keithstrachan/Tiny-M/STLs/essentials/Gantry/Front-Idler/readme.md

# Front Idler V4  

- optimzed belt path
- fixed printing 0.2 layer high

## BOM  
4 x F695-2RS  
2 x DIN 912 M5x40  
2 x ISO 7380-1 V2 M5x35  
2 x M5 T-Nut  
2 x ISO 7380-1 M5x16  

**Washer Variante 1:**  
4 x DIN 988 5x10x1 Shim Ring  

**Washer Variante 2:**   (0.5mm washer between bearings):  
2 x DIN 988 5x8x0.5 Shim Ring  
4 x DIN 988 5x8x0.75 Shim Ring
