keithstrachan/Tiny-M/images/v4_toolhead.jpg

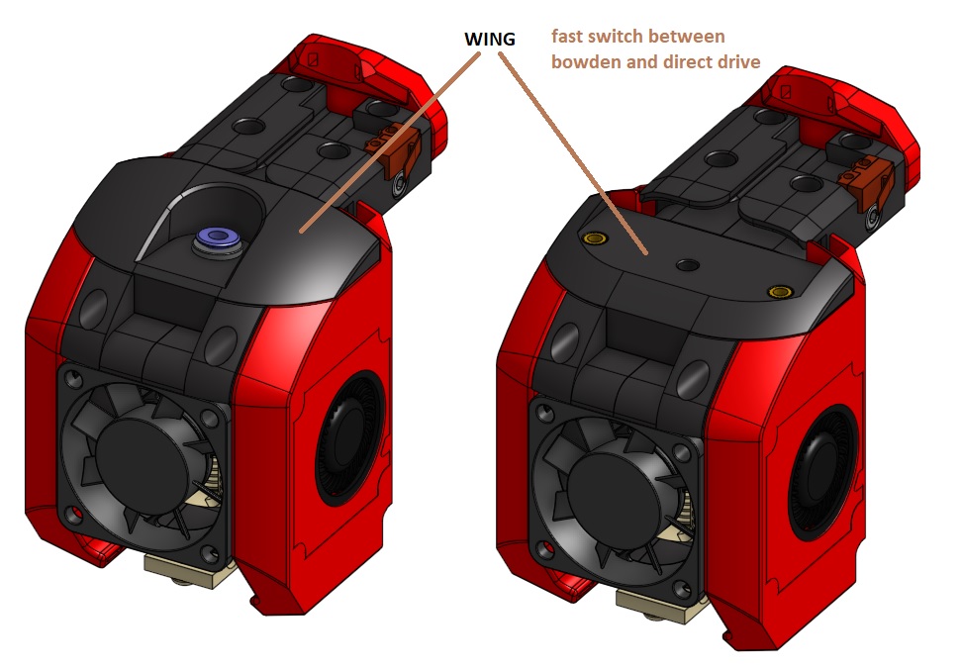
images/v4_toolhead.jpg
