keithstrachan/Tiny-M/usermods/almost_all_metal_undercarriage_with_purge_bucket/Images/image_under_1.jpg

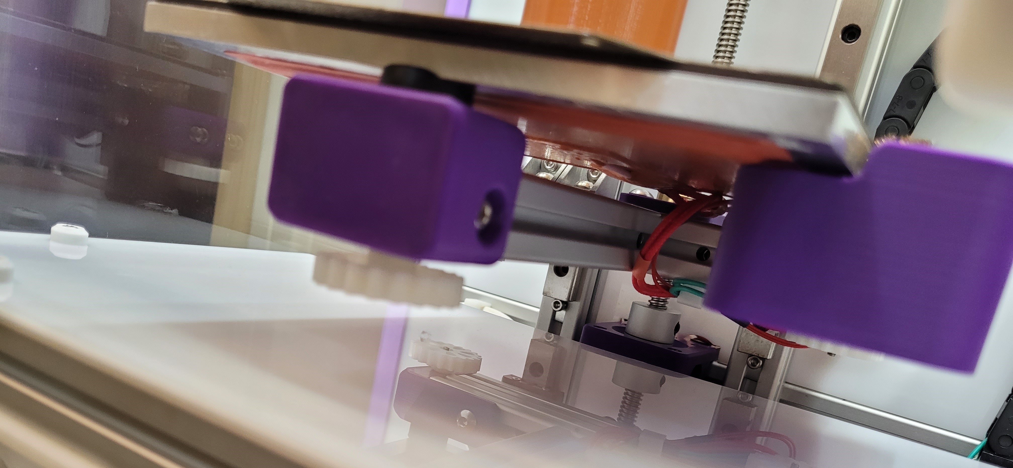
usermods/almost_all_metal_undercarriage_with_purge_bucket/Images/image_under_1.jpg
