keithstrachan/Tiny-M/usermods/belted_z_mod/Images/Above bed.jpg

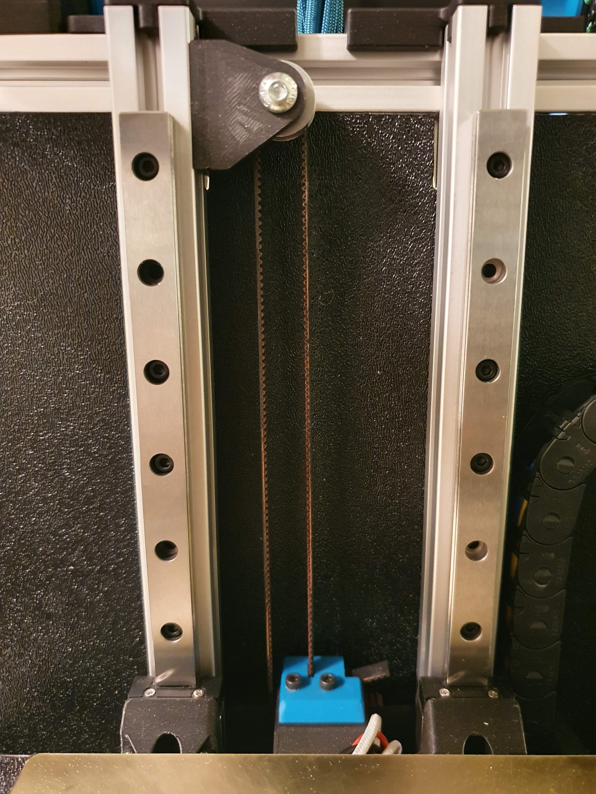
usermods/belted_z_mod/Images/Above bed.jpg
