keithstrachan/Tiny-M/usermods/belted_z_mod/Images/CAD front.png

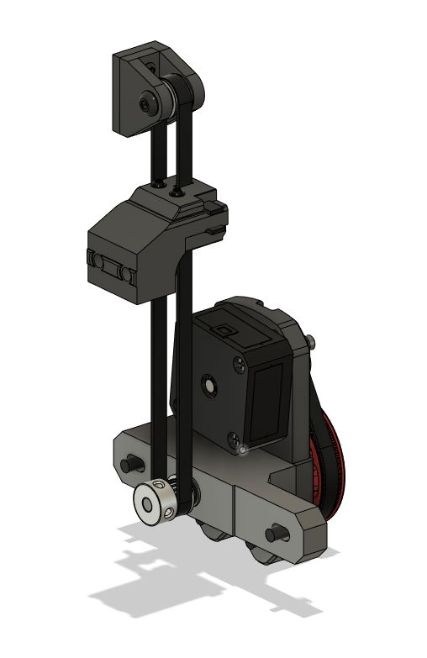
usermods/belted_z_mod/Images/CAD front.png
