keithstrachan/Tiny-M/usermods/belted_z_mod/Images/Motor.jpg

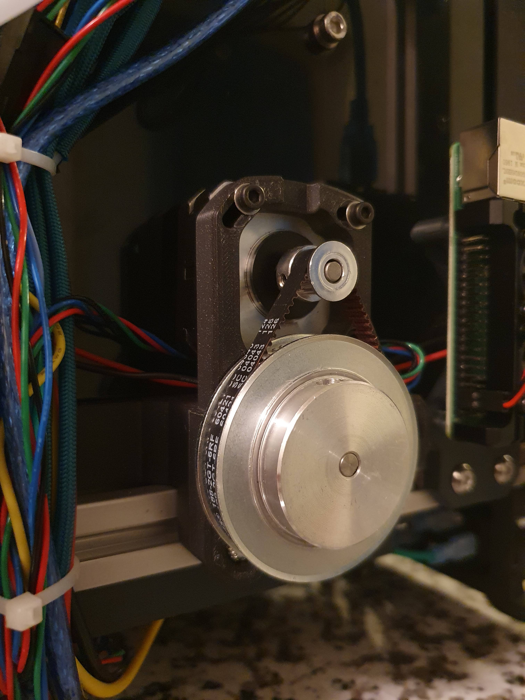
usermods/belted_z_mod/Images/Motor.jpg
