keithstrachan/Tiny-M/usermods/high_torque_belted_z/images/20210530_182317.jpg

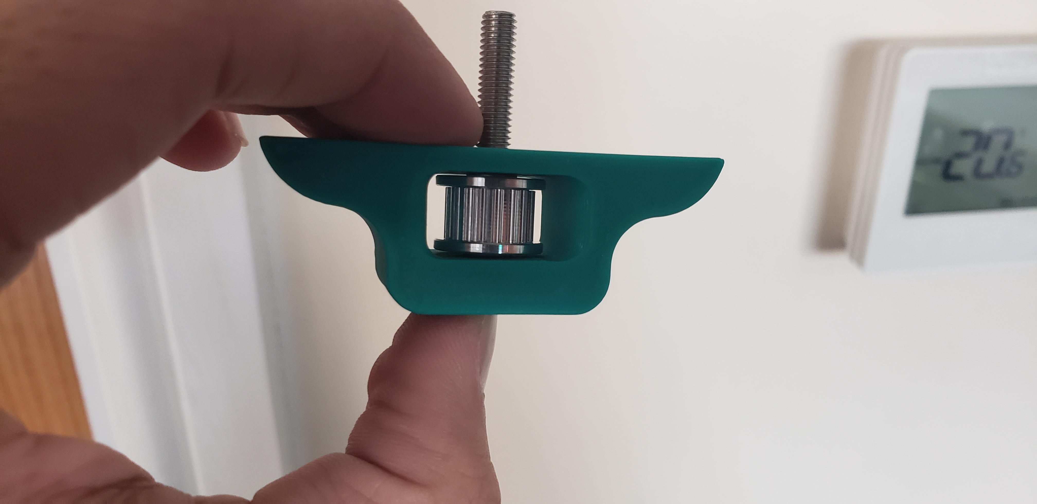
usermods/high_torque_belted_z/images/20210530_182317.jpg
