keithstrachan/Tiny-M/usermods/high_torque_belted_z/images/20210605_135525.jpg

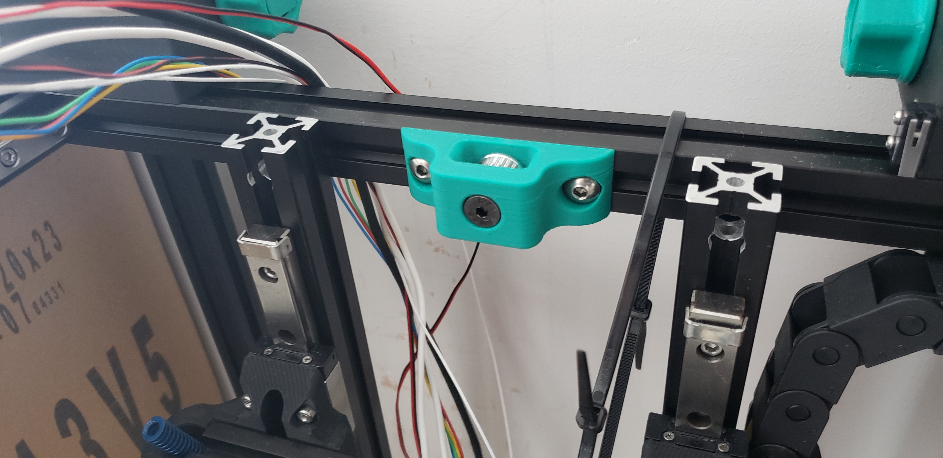
usermods/high_torque_belted_z/images/20210605_135525.jpg
