keithstrachan/Tiny-M/usermods/high_torque_belted_z/images/20210607_204112.jpg

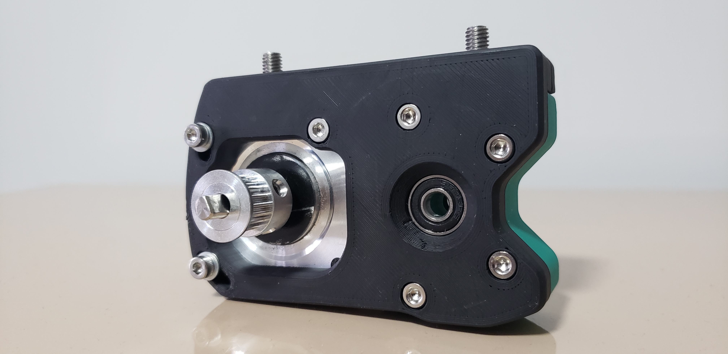
usermods/high_torque_belted_z/images/20210607_204112.jpg
