keithstrachan/Tiny-M/usermods/high_torque_belted_z/images/20210608_170528.jpg

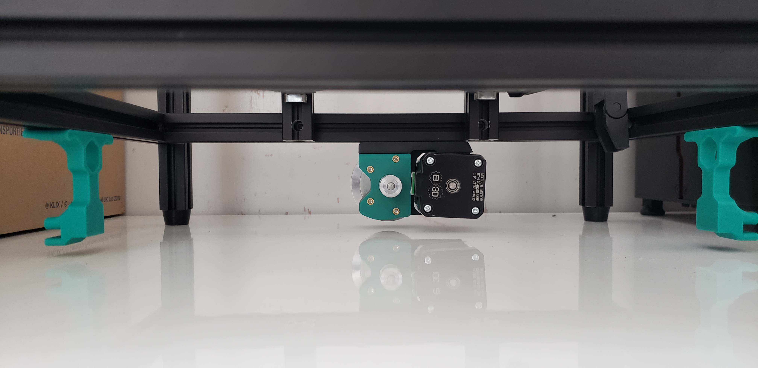
usermods/high_torque_belted_z/images/20210608_170528.jpg
