keithstrachan/Tiny-M/usermods/high_torque_belted_z/images/20210608_170559.jpg

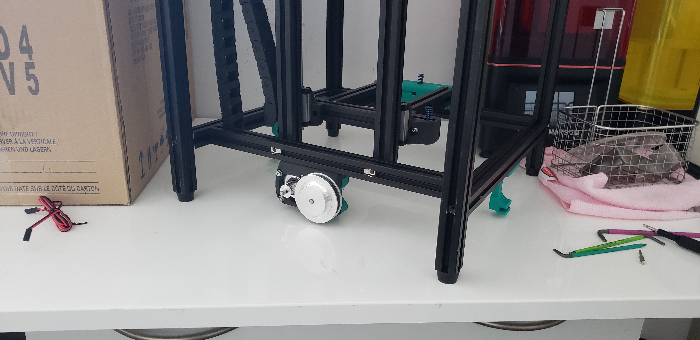
usermods/high_torque_belted_z/images/20210608_170559.jpg
