keithstrachan/Tiny-M/usermods/high_torque_belted_z/images/20210618_183542.jpg

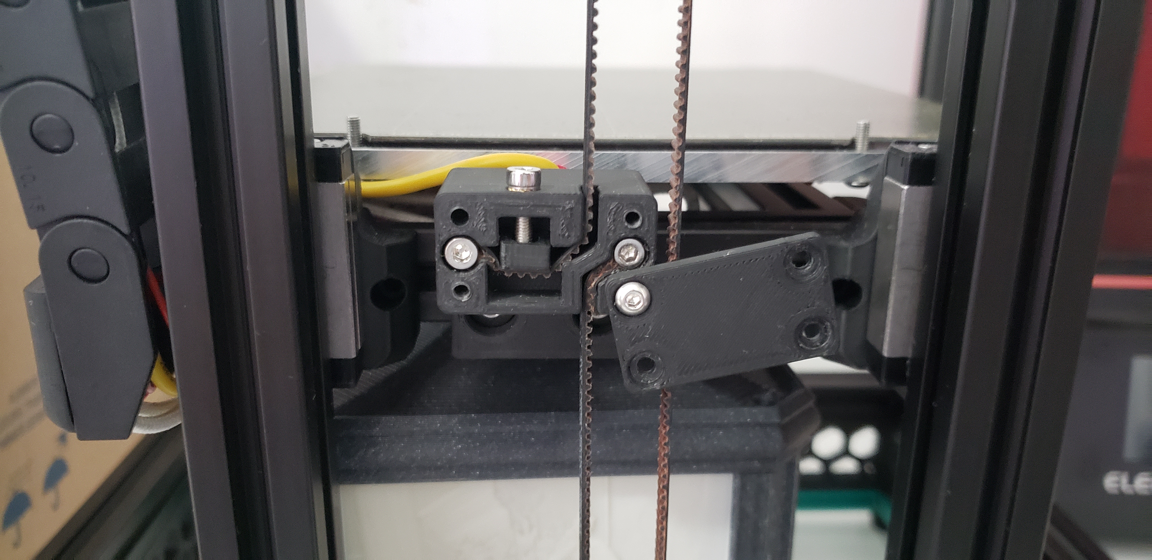
usermods/high_torque_belted_z/images/20210618_183542.jpg
