keithstrachan/Tiny-M/usermods/high_torque_belted_z/images/Fusion360_Lnw4iSIMuG.png

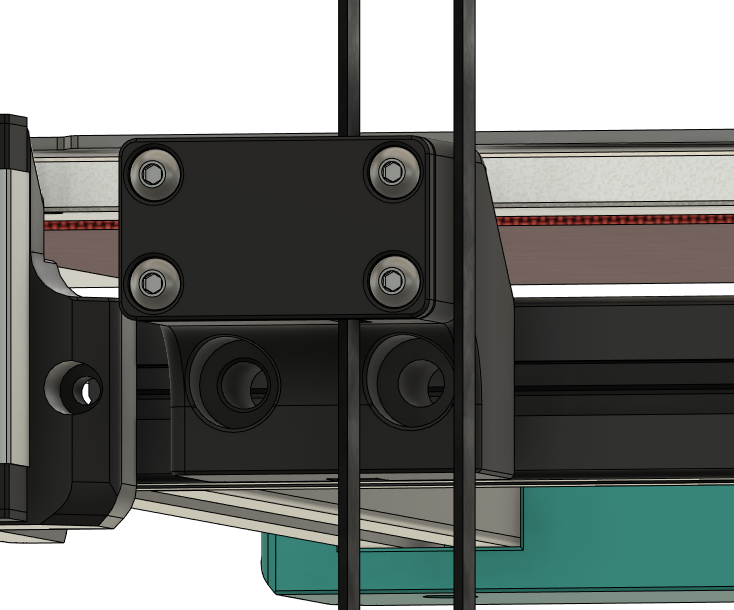
usermods/high_torque_belted_z/images/Fusion360_Lnw4iSIMuG.png
