keithstrachan/Tiny-M/usermods/DrillGuides/tiny-m_drill_guide.step.step

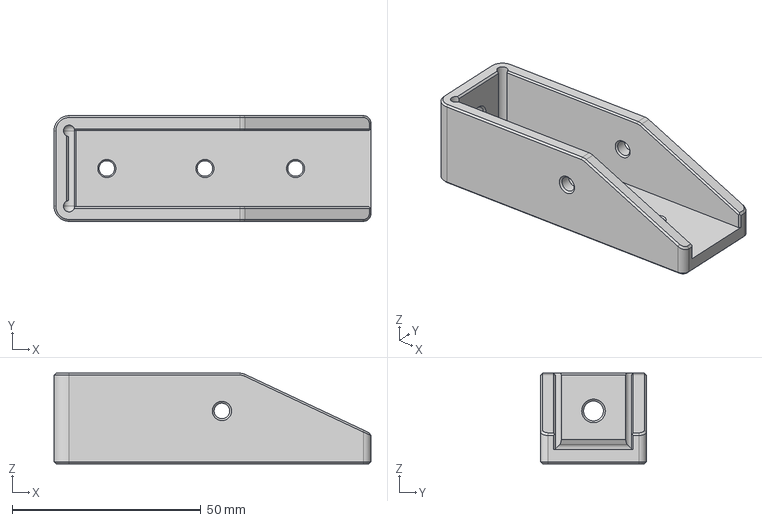
[picture p43: CAD file, 2021-09-06]
usermods/DrillGuides/tiny-m_drill_guide.step.step
84.0 x 28.0 x 24.0 mm
