keithstrachan/Tiny-M/usermods/front_bed_mount_proud_text.stl

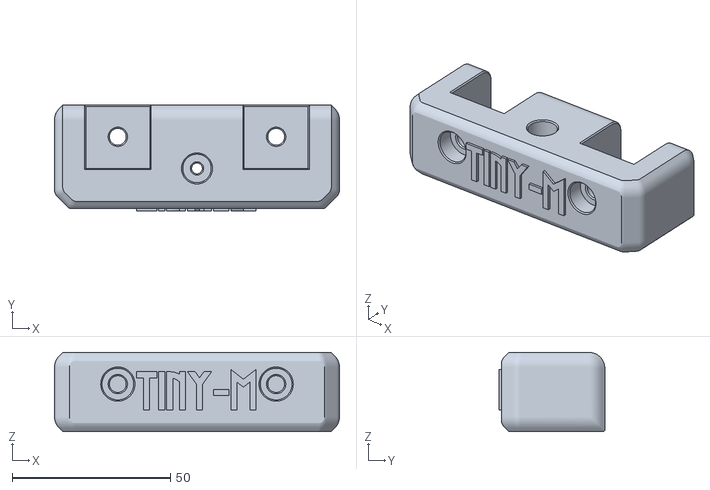
[picture p44: CAD file, 2021-03-21]
usermods/front_bed_mount_proud_text.stl
90.0 x 33.4 x 25.0
