keithstrachan/Tiny-M/usermods/high_torque_belted_z/STLs/150mm ver/beltztens150.stl

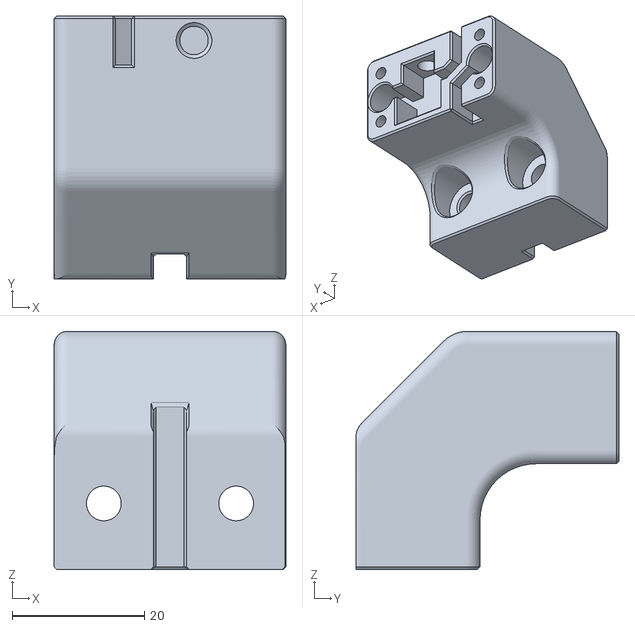
[picture p45: CAD file, 2021-12-28]
usermods/high_torque_belted_z/STLs/150mm ver/beltztens150.stl
35.0 x 39.7 x 36.0
