keithstrachan/Tiny-M/usermods/high_torque_belted_z/STLs/[a]_upper_idler.stl

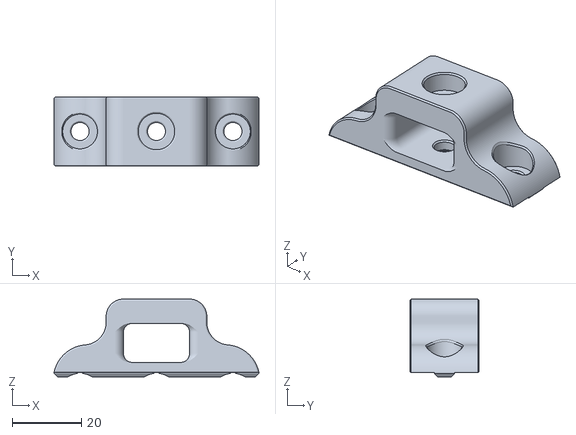
[picture p46: CAD file, 2021-09-06]
usermods/high_torque_belted_z/STLs/[a]_upper_idler.stl
59.0 x 20.0 x 22.4
