keithstrachan/Tiny-M/usermods/mgn12_x_rail/Tiny-M_Umbilical_Frame.stl

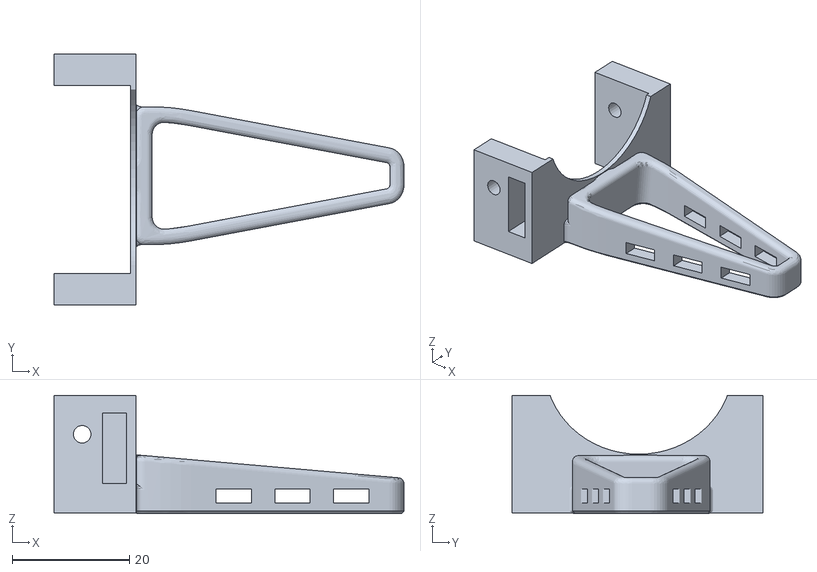
[picture p47: CAD file, 2021-03-21]
usermods/mgn12_x_rail/Tiny-M_Umbilical_Frame.stl
59.6 x 42.7 x 20.1
