keithstrachan/Tiny-M/usermods/rear_cable_guide/right-back-cable-holder-honeycomb.stl

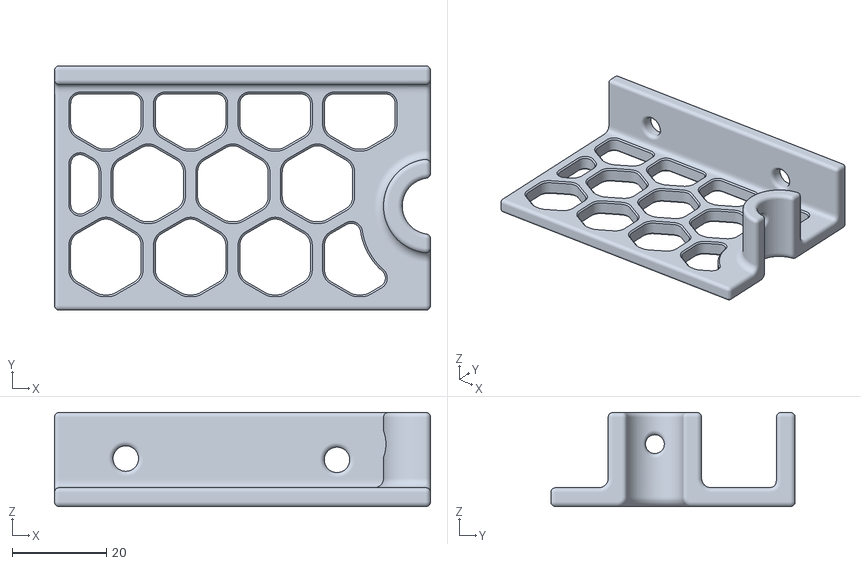
[picture p48: CAD file, 2021-04-13]
usermods/rear_cable_guide/right-back-cable-holder-honeycomb.stl
80.0 x 52.0 x 20.0
