keithstrachan/Tiny-M/usermods/Tiny-dooM/STL/DoomCap.stl

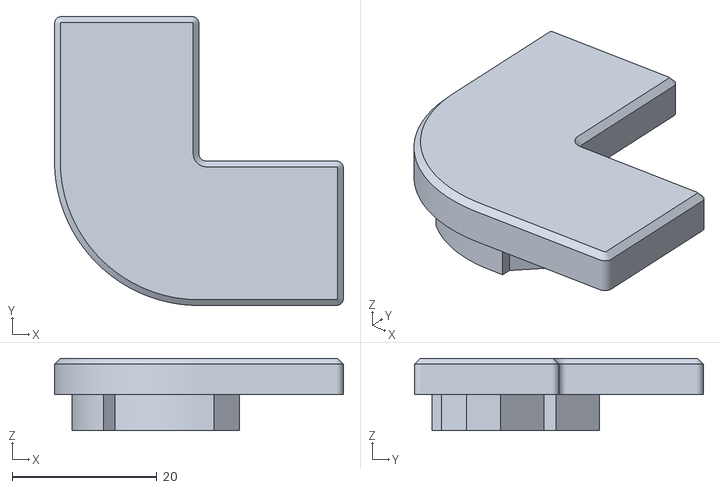
[picture p49: CAD file, 2021-05-16]
usermods/Tiny-dooM/STL/DoomCap.stl
40.0 x 40.0 x 10.0
