keithstrachan/Tiny-M/usermods/triple_z_belted/STL/motor_mount_x3.stl

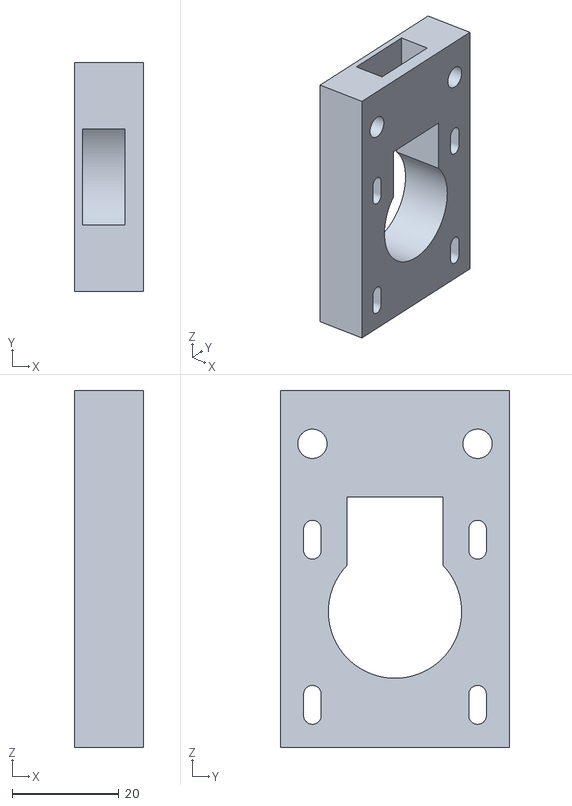
[picture p50: CAD file, 2021-05-16]
usermods/triple_z_belted/STL/motor_mount_x3.stl
13.0 x 43.0 x 67.0
