keithstrachan/Tiny-M/usermods/Xile_Mods/Buck_Converter_Mount/Buck_Converter_Mount.STL

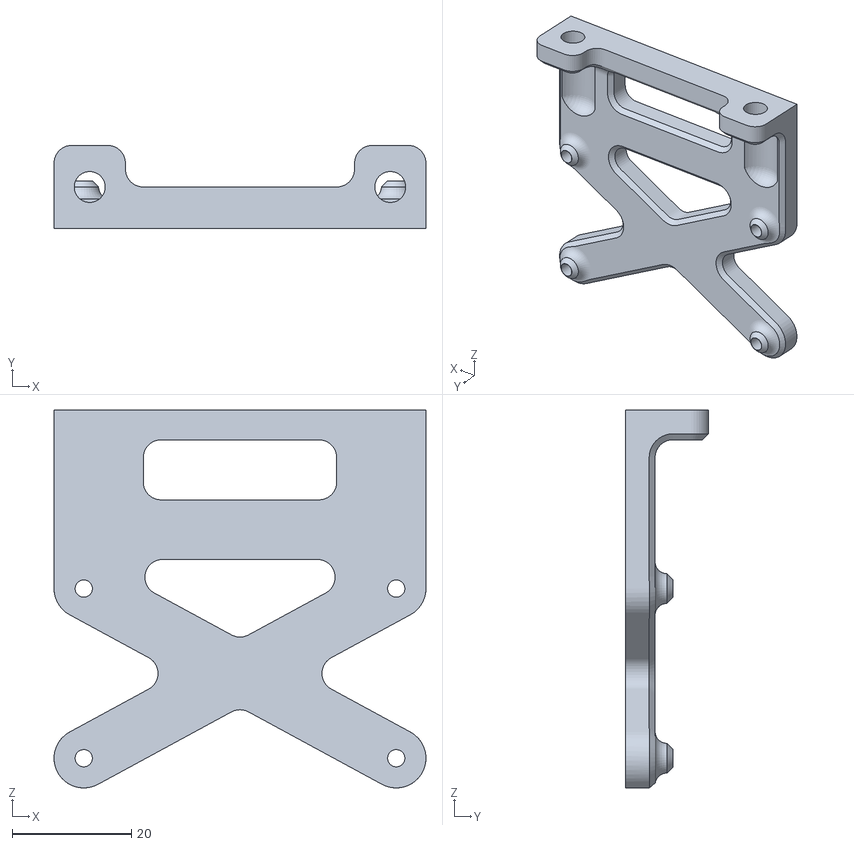
[picture p51: CAD file, 2021-03-21]
usermods/Xile_Mods/Buck_Converter_Mount/Buck_Converter_Mount.STL
62.5 x 14.0 x 63.5
