keithstrachan/Tiny-M/usermods/Xile_Mods/Cover_No_Logo.stl

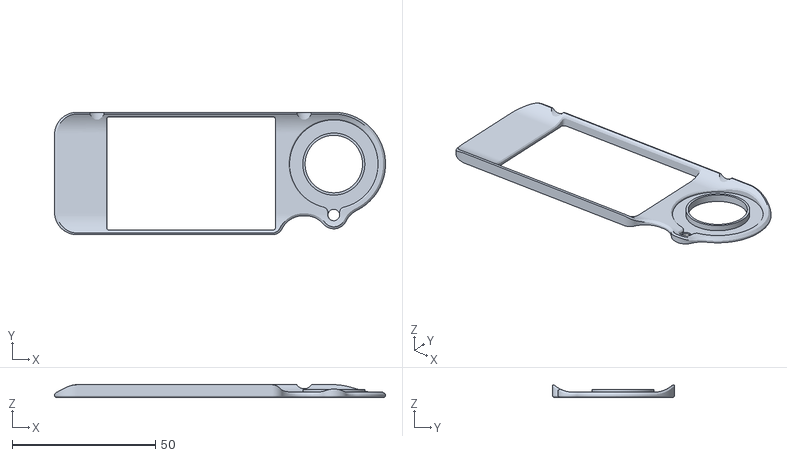
[picture p52: CAD file, 2021-03-21]
usermods/Xile_Mods/Cover_No_Logo.stl
115.4 x 42.6 x 4.42
