keithstrachan/Tiny-M/usermods/Xile_Mods/LRS-150_Mount/LRS-150_Mount.STL

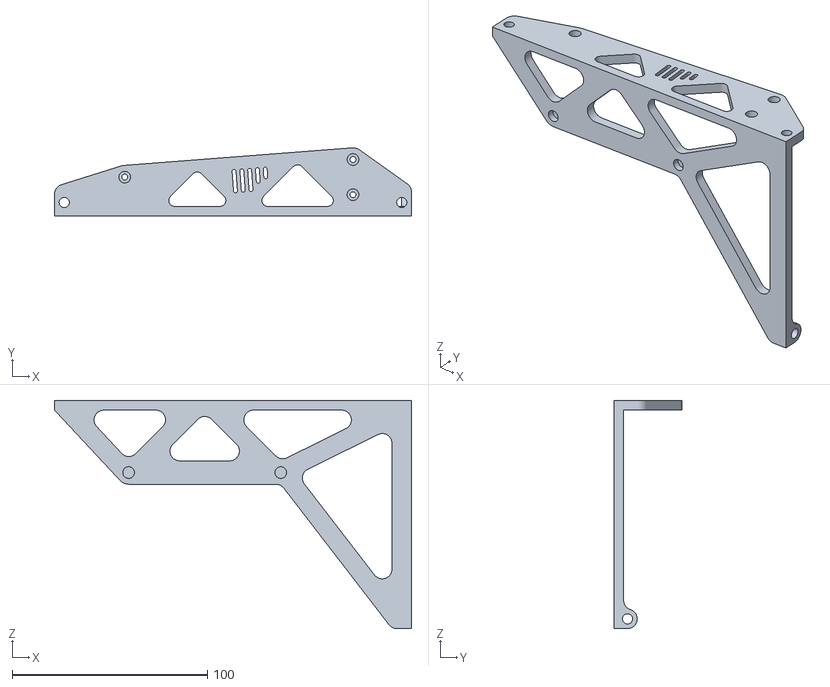
[picture p53: CAD file, 2021-03-21]
usermods/Xile_Mods/LRS-150_Mount/LRS-150_Mount.STL
183.0 x 35.0 x 117.0
