keithstrachan/Tiny-M/usermods/Xile_Mods/Panel Mounting/PanelClip_v2_1.stl

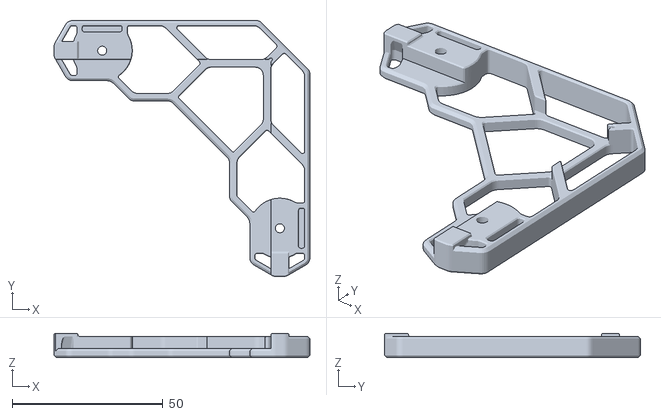
[picture p54: CAD file, 2021-03-21]
usermods/Xile_Mods/Panel Mounting/PanelClip_v2_1.stl
85.0 x 85.0 x 8.10
