keithstrachan/Tiny-M/usermods/Xile_Mods/Raised_ABdrives/ab_drive_top_raised.STL

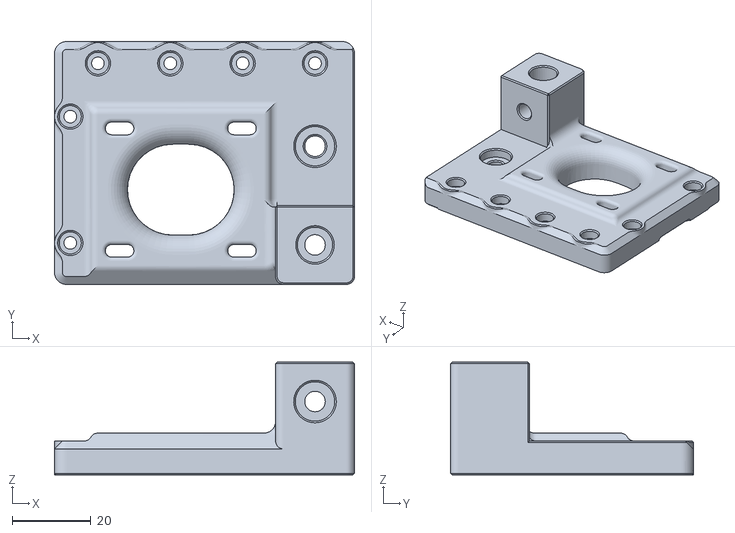
[picture p55: CAD file, 2021-03-21]
usermods/Xile_Mods/Raised_ABdrives/ab_drive_top_raised.STL
76.0 x 61.5 x 28.6
