keithstrachan/Tiny-M/usermods/Xile_Mods/Raspi_Mount/Raspi_Mount.STL

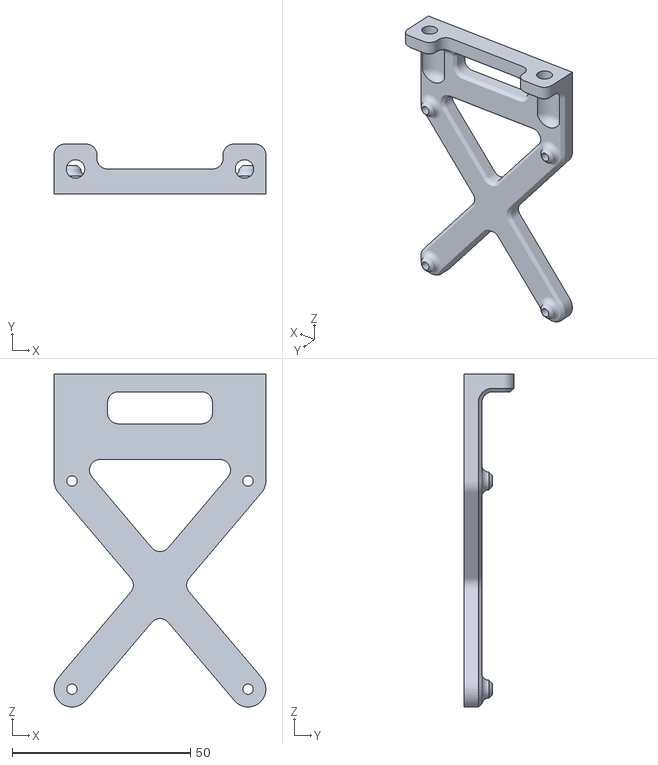
[picture p56: CAD file, 2021-03-21]
usermods/Xile_Mods/Raspi_Mount/Raspi_Mount.STL
59.4 x 14.0 x 93.4
