keithstrachan/Tiny-M/usermods/Xile_Mods/SKR_Mini_Mount/SKR_Mini_Mount.STL

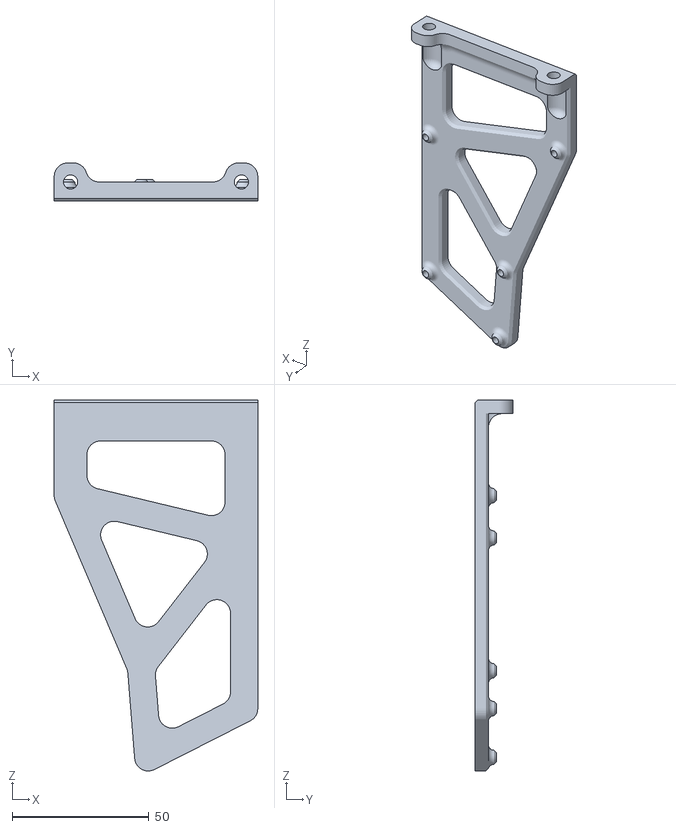
[picture p57: CAD file, 2021-03-21]
usermods/Xile_Mods/SKR_Mini_Mount/SKR_Mini_Mount.STL
74.5 x 14.0 x 135.8
