keithstrachan/Tiny-M/usermods/Xile_Mods/Tensioning_Wrench/Knob_Wrench.stl

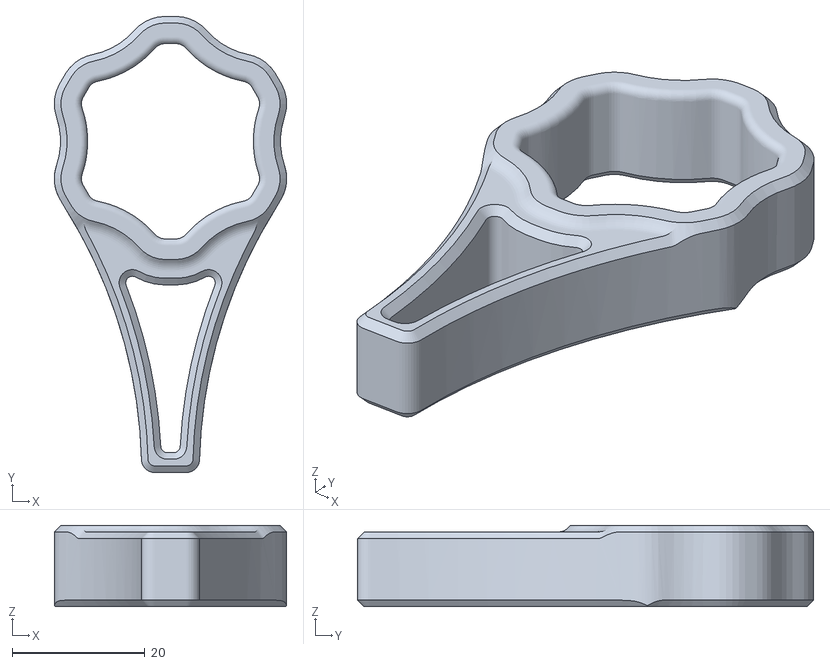
[picture p58: CAD file, 2021-03-21]
usermods/Xile_Mods/Tensioning_Wrench/Knob_Wrench.stl
35.1 x 68.8 x 12.3
