keithstrachan/Tiny-M/CAD/V4/Drill Tap Jigs v4.step

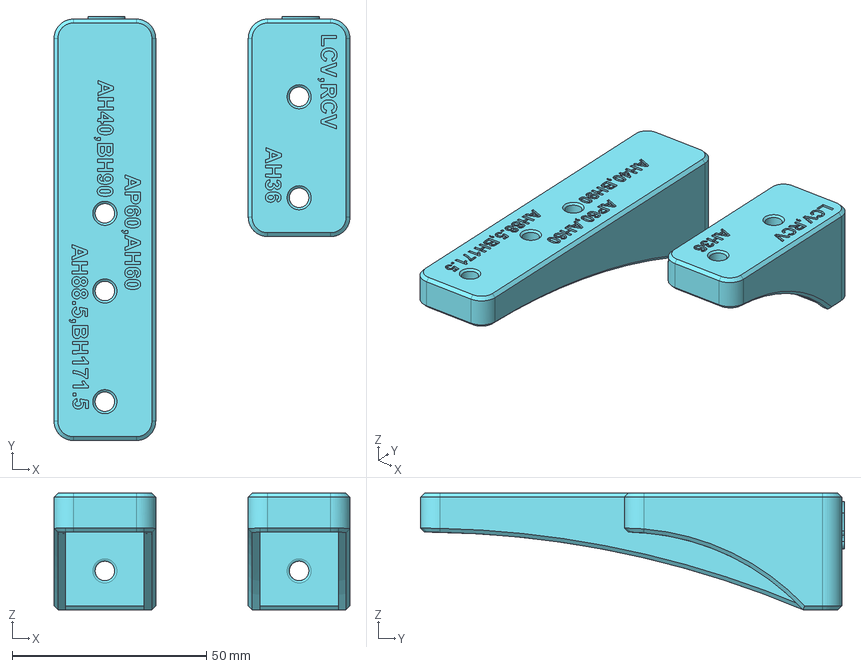
[picture p59: CAD file, 2021-05-12]
CAD/V4/Drill Tap Jigs v4.step
76.2 x 109.2 x 30.0 mm
