keithstrachan/Tiny-M/STLs/essentials/Bed/z_position_lower.stl

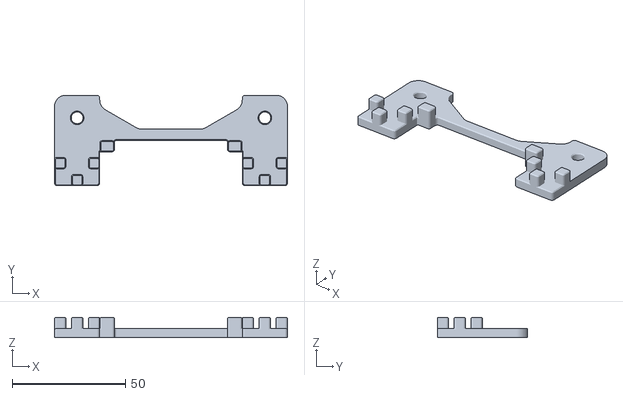
[picture p60: CAD file, 2021-05-06]
STLs/essentials/Bed/z_position_lower.stl
103.0 x 40.0 x 9.00
