keithstrachan/Tiny-M/STLs/essentials/Gantry/X_Axis/X_Carriage/mini_AB_parts/printed_parts_MGN12_v4 - mini_ab - latch_shuttle.stl

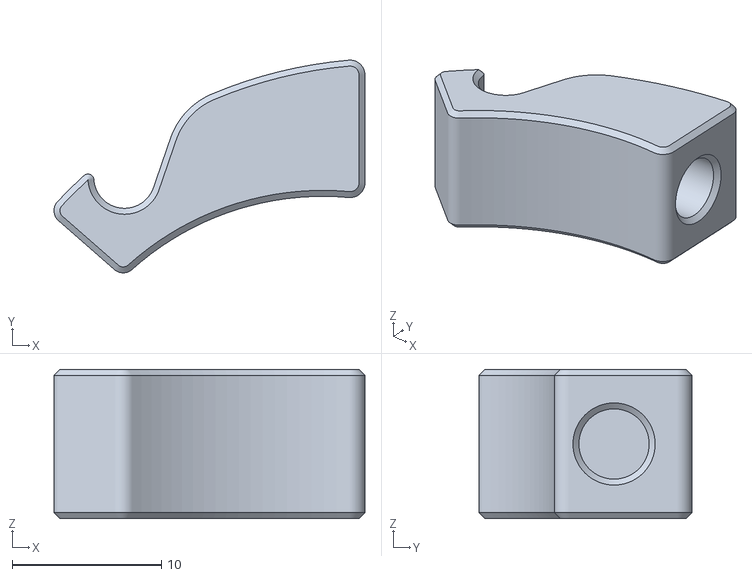
[picture p61: CAD file, 2021-05-06]
STLs/essentials/Gantry/X_Axis/X_Carriage/mini_AB_parts/printed_parts_MGN12_v4 - mini_ab - latch_shuttle.stl
20.8 x 14.2 x 10.0
