keithstrachan/Tiny-M/STLs/essentials/Gantry/X_Axis/X_Carriage/x-carriage_belt_clamp.stl

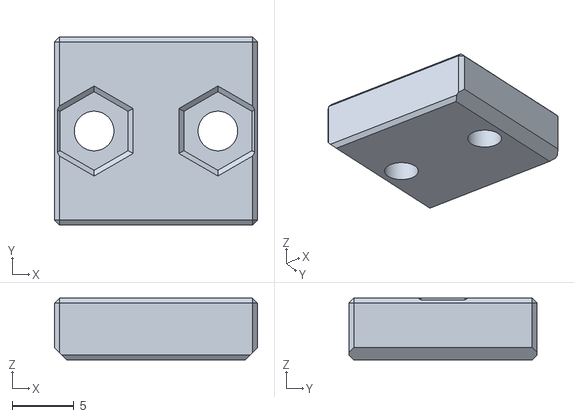
[picture p62: CAD file, 2021-05-06]
STLs/essentials/Gantry/X_Axis/X_Carriage/x-carriage_belt_clamp.stl
16.4 x 15.2 x 5.00
