keithstrachan/Tiny-M/STLs/essentials/Tools/Drill_Tap_Jig_A_.stl

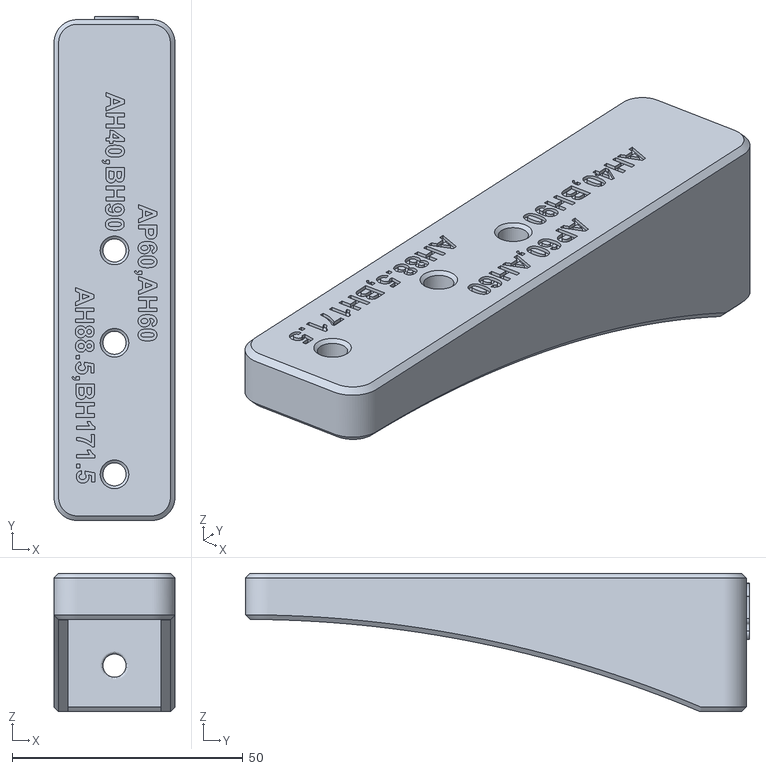
[picture p63: CAD file, 2021-05-12]
STLs/essentials/Tools/Drill_Tap_Jig_A_.stl
26.2 x 109.2 x 30.0
