keithstrachan/Tiny-M/usermods/190mm_prusa_mini_mod/STLs/[a]_side_skirt_right_x2.stl

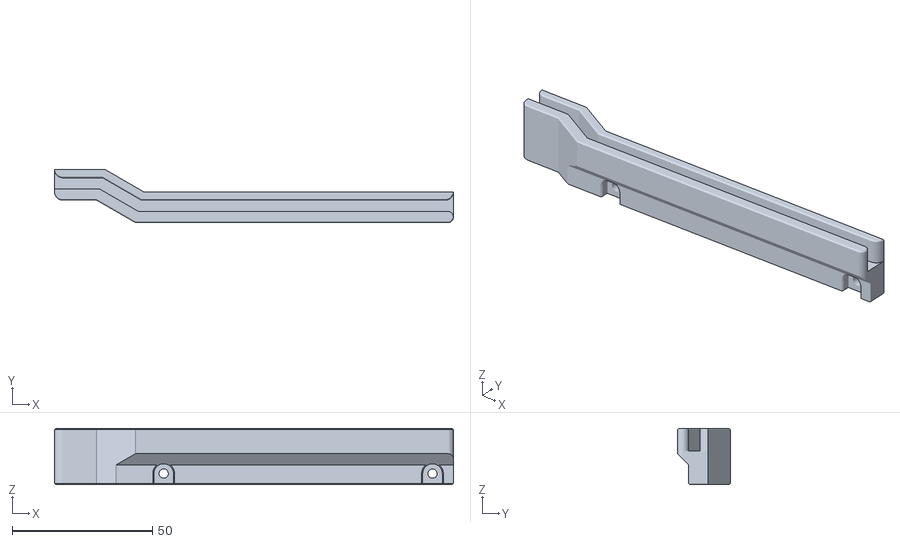
[picture p64: CAD file, 2021-05-06]
usermods/190mm_prusa_mini_mod/STLs/[a]_side_skirt_right_x2.stl
142.5 x 19.0 x 20.0
