keithstrachan/Tiny-M/usermods/2020_Hinged_TopHat_Print/2020_Hinged_TopHat_Print_Hinge Mid 2 Print.stl

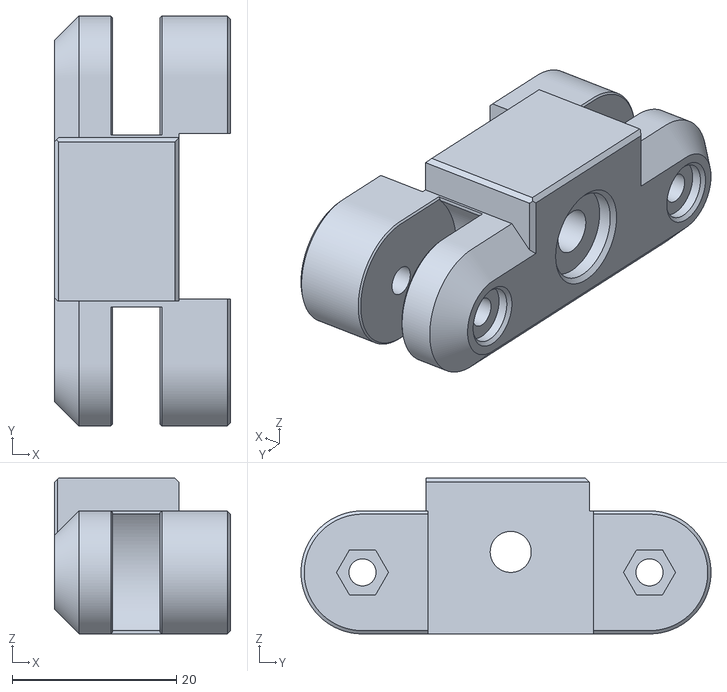
[picture p65: CAD file, 2021-03-21]
usermods/2020_Hinged_TopHat_Print/2020_Hinged_TopHat_Print_Hinge Mid 2 Print.stl
21.5 x 50.0 x 19.0
