keithstrachan/Tiny-M/usermods/5mm_idler_pins/CAD/front_idler_right_V4_5mm_Pin v3.step

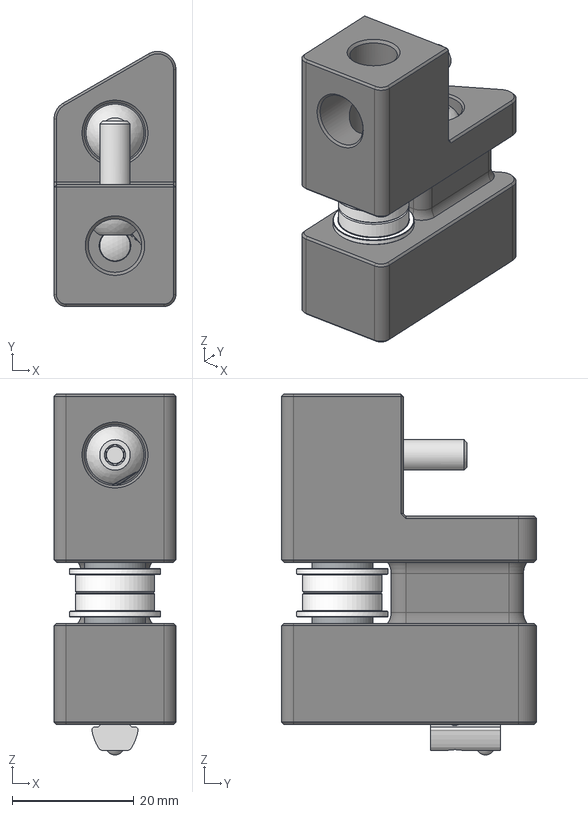
[picture p66: CAD file, 2021-03-31]
usermods/5mm_idler_pins/CAD/front_idler_right_V4_5mm_Pin v3.step
20.0 x 41.8 x 59.2 mm
F695-2RS x 2
ISO 7380-1 M5x35
DIN 988 5x10x1 Shim Ring x 2
front_idler_right_bottom_V4
M5x16
M5-T-Nut
front_idler_right_top_V4
91595A376_32mm_METRIC ALLOY STEEL DOWEL PIN
