keithstrachan/Tiny-M/usermods/all_metal_bed_undercarriage/CAD/190_bed.step

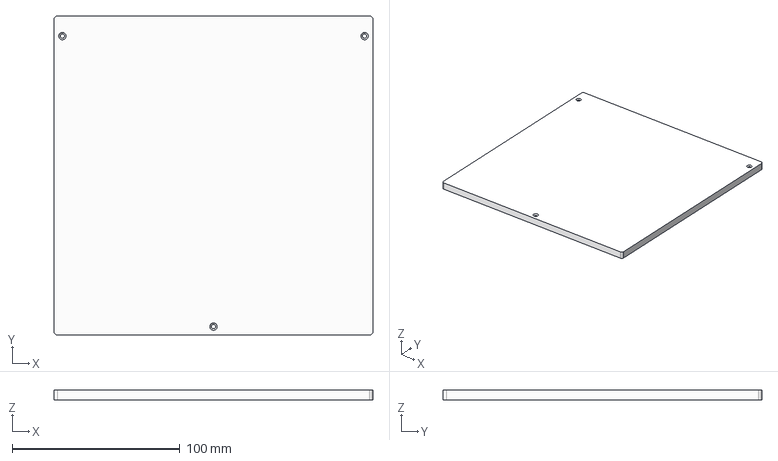
[picture p67: CAD file, 2021-05-21]
usermods/all_metal_bed_undercarriage/CAD/190_bed.step
190.0 x 190.0 x 6.00 mm
