keithstrachan/Tiny-M/usermods/all_metal_bed_undercarriage/STL/middle_jig.stl

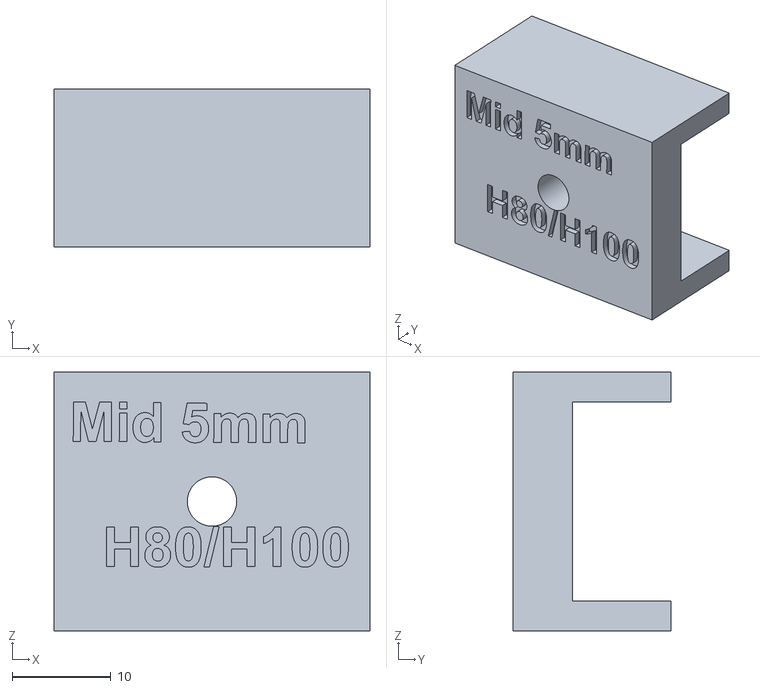
[picture p68: CAD file, 2021-05-21]
usermods/all_metal_bed_undercarriage/STL/middle_jig.stl
32.0 x 16.0 x 26.2
