keithstrachan/Tiny-M/usermods/almost_all_metal_undercarriage_with_purge_bucket/STLs/bed_right_mount.3mf

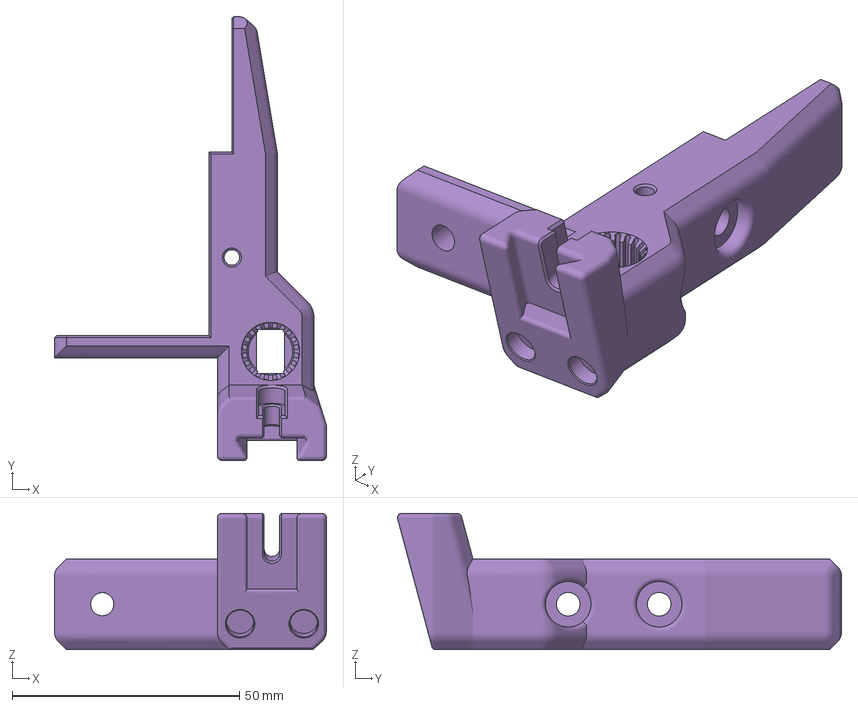
[picture p69: CAD file, 2021-12-28]
usermods/almost_all_metal_undercarriage_with_purge_bucket/STLs/bed_right_mount.3mf
59.8 x 97.6 x 30.0 mm
