keithstrachan/Tiny-M/usermods/belted_z_mod/STLs/Pancake Stepper Bracket.stl

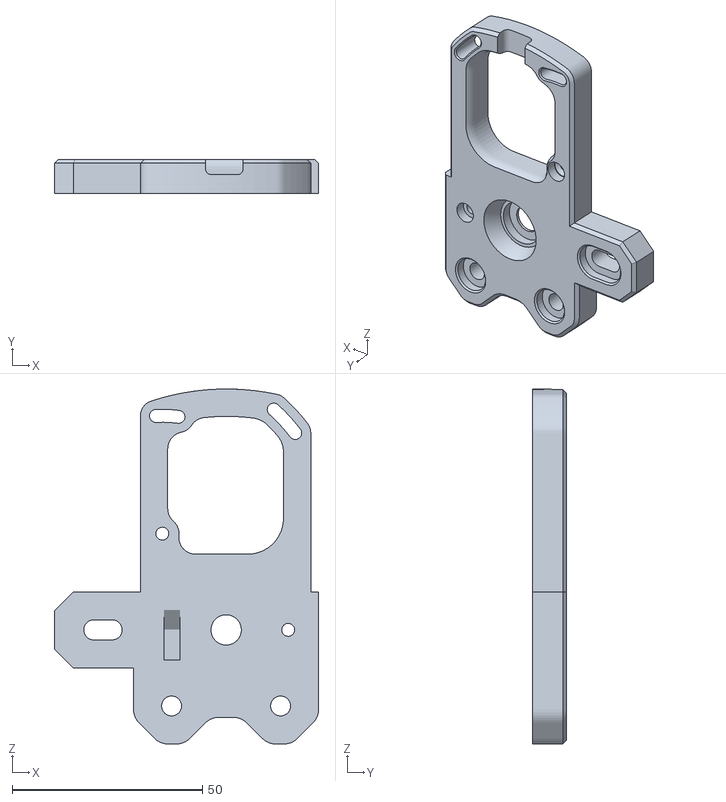
[picture p70: CAD file, 2021-05-12]
usermods/belted_z_mod/STLs/Pancake Stepper Bracket.stl
69.5 x 9.00 x 93.3
