keithstrachan/Tiny-M/usermods/door_handle/stl/Door_Handle.stl

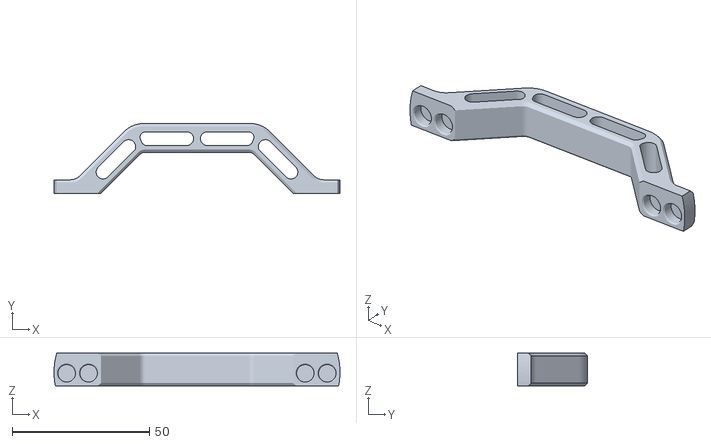
[picture p71: CAD file, 2022-09-30]
usermods/door_handle/stl/Door_Handle.stl
104.3 x 25.5 x 12.0
