keithstrachan/Tiny-M/usermods/DrillGuides/tiny-m_tap_guide.step

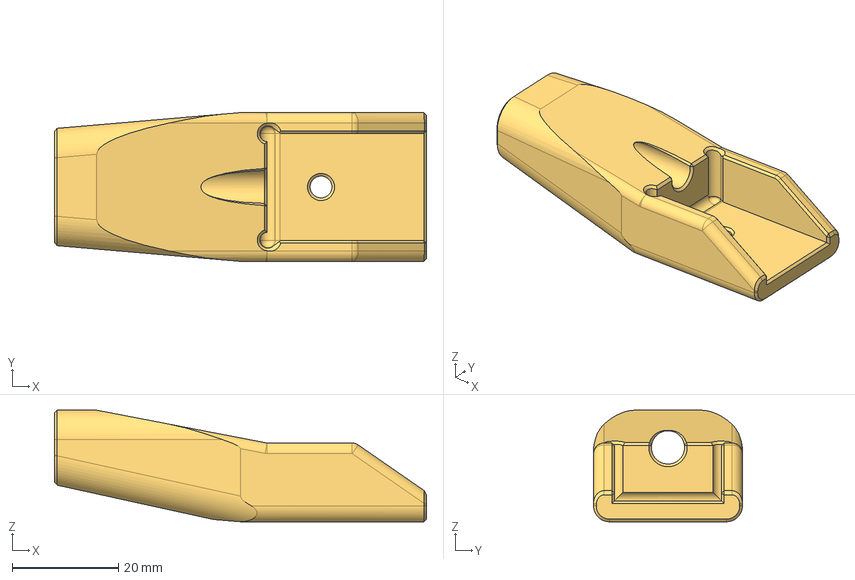
[picture p72: CAD file, 2021-09-06]
usermods/DrillGuides/tiny-m_tap_guide.step
70.0 x 28.0 x 21.0 mm
