keithstrachan/Tiny-M/usermods/high_torque_belted_z/STLs/150mm ver/idlerm5p2.stl

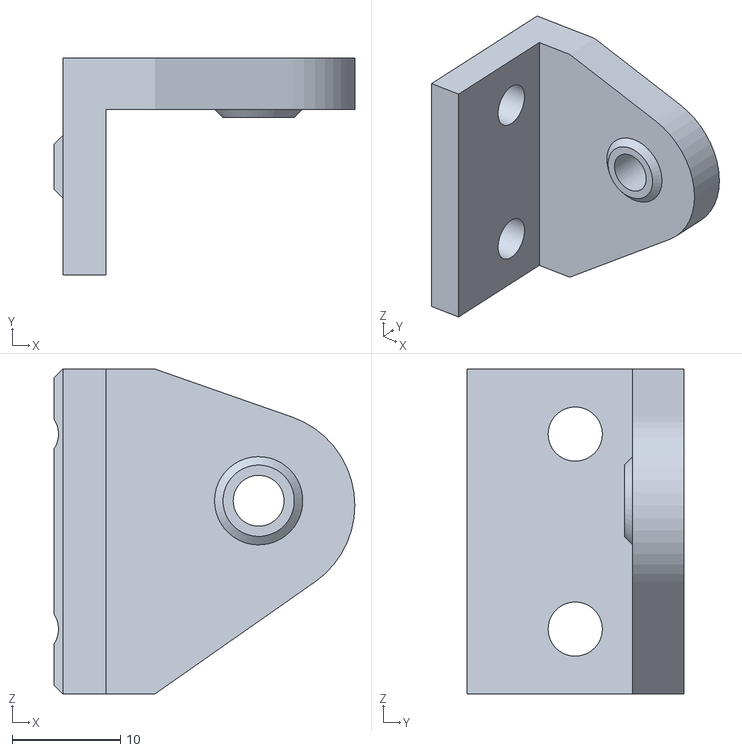
[picture p73: CAD file, 2021-12-28]
usermods/high_torque_belted_z/STLs/150mm ver/idlerm5p2.stl
27.8 x 20.0 x 30.0
