keithstrachan/Tiny-M/usermods/high_torque_belted_z/STLs/[a]_tension_plate.stl

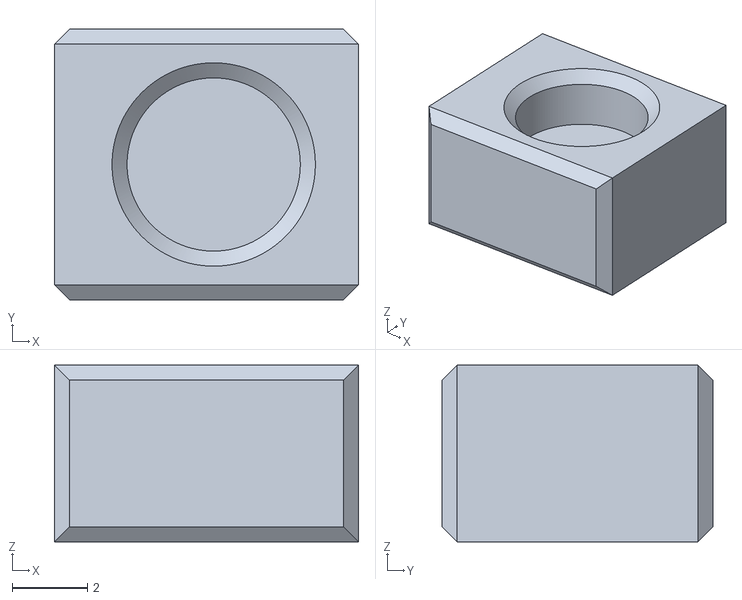
[picture p74: CAD file, 2021-09-06]
usermods/high_torque_belted_z/STLs/[a]_tension_plate.stl
8.07 x 7.20 x 4.70
