keithstrachan/Tiny-M/usermods/mgn12_x_rail/Tiny-M_Extruder_for_Sherpa_Mini__MGN12H.stl

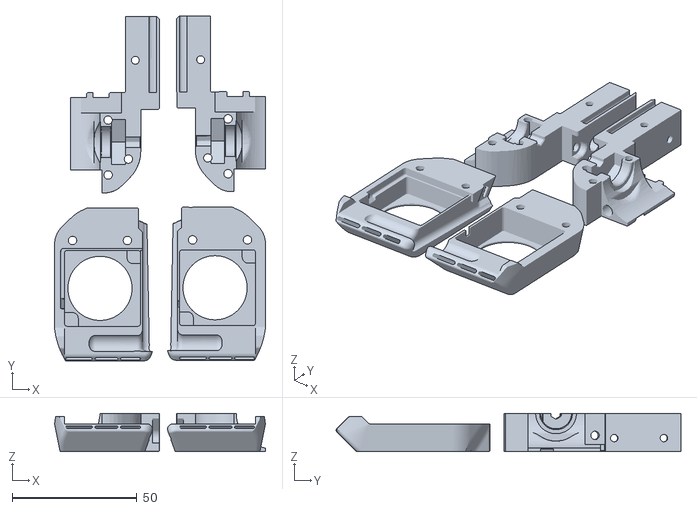
[picture p75: CAD file, 2021-03-21]
usermods/mgn12_x_rail/Tiny-M_Extruder_for_Sherpa_Mini__MGN12H.stl
84.6 x 138.2 x 15.4
