keithstrachan/Tiny-M/usermods/rear_cable_guide/back-cable-holder-honeycomb.step

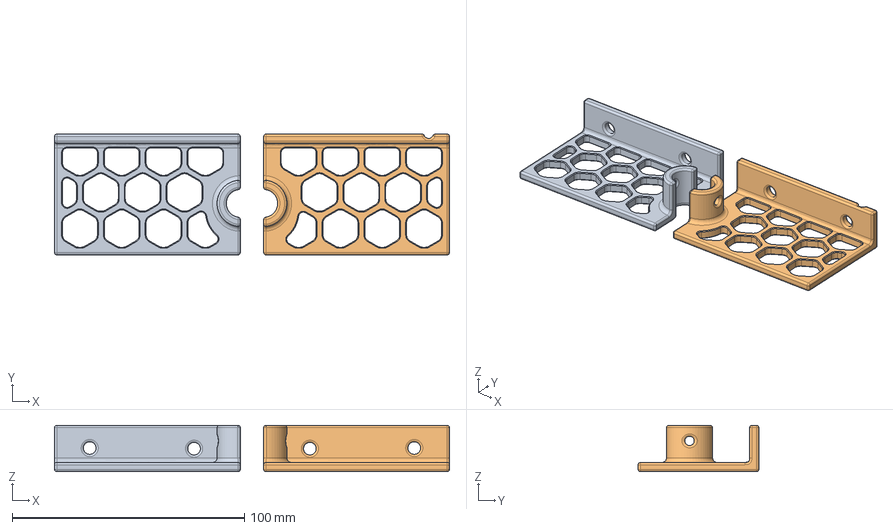
[picture p76: CAD file, 2021-04-13]
usermods/rear_cable_guide/back-cable-holder-honeycomb.step
170.1 x 52.0 x 20.0 mm
