keithstrachan/Tiny-M/usermods/Tiny-dooM/STL/DoomFoot.stl

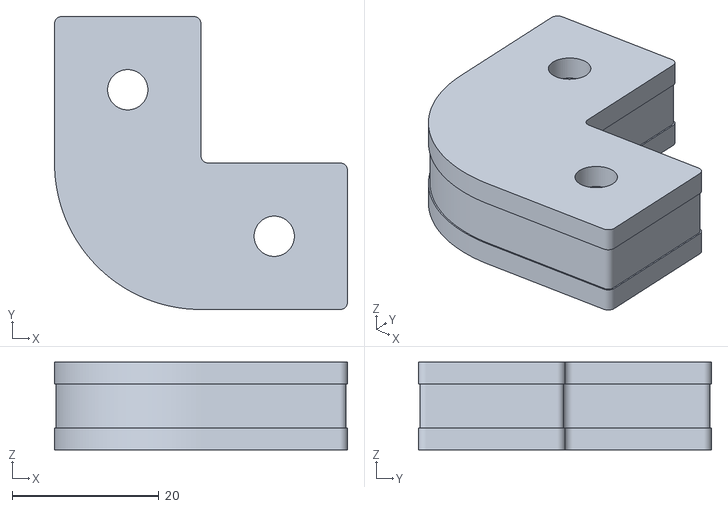
[picture p77: CAD file, 2021-05-16]
usermods/Tiny-dooM/STL/DoomFoot.stl
40.0 x 40.0 x 12.0
