keithstrachan/Tiny-M/usermods/triple_z_belted/STL/lifter_left_rear_x2.stl

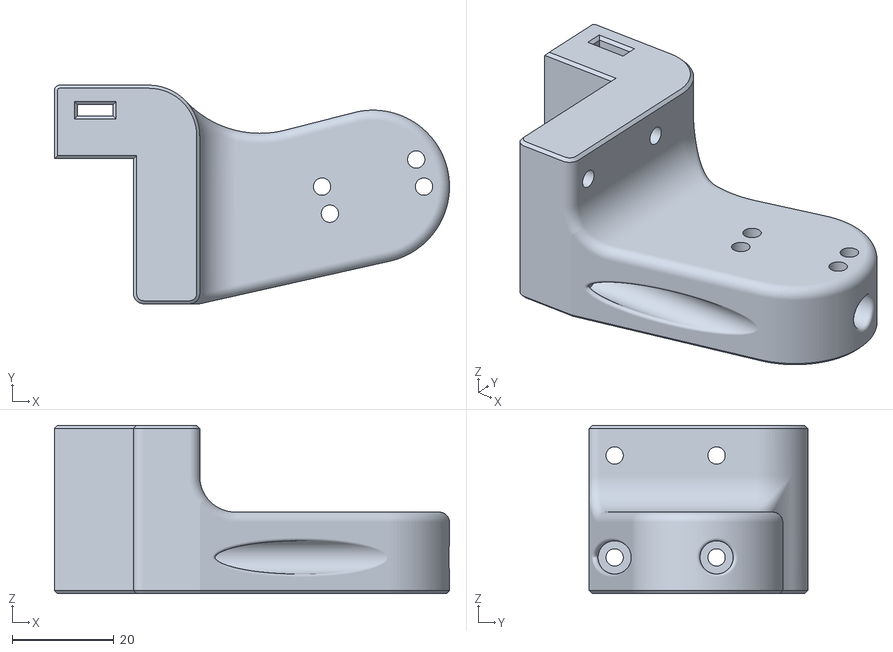
[picture p78: CAD file, 2021-05-16]
usermods/triple_z_belted/STL/lifter_left_rear_x2.stl
77.5 x 42.9 x 33.0
