keithstrachan/Tiny-M/usermods/Xile_Mods/Panel Mounting/Panel_Holder_1.STL

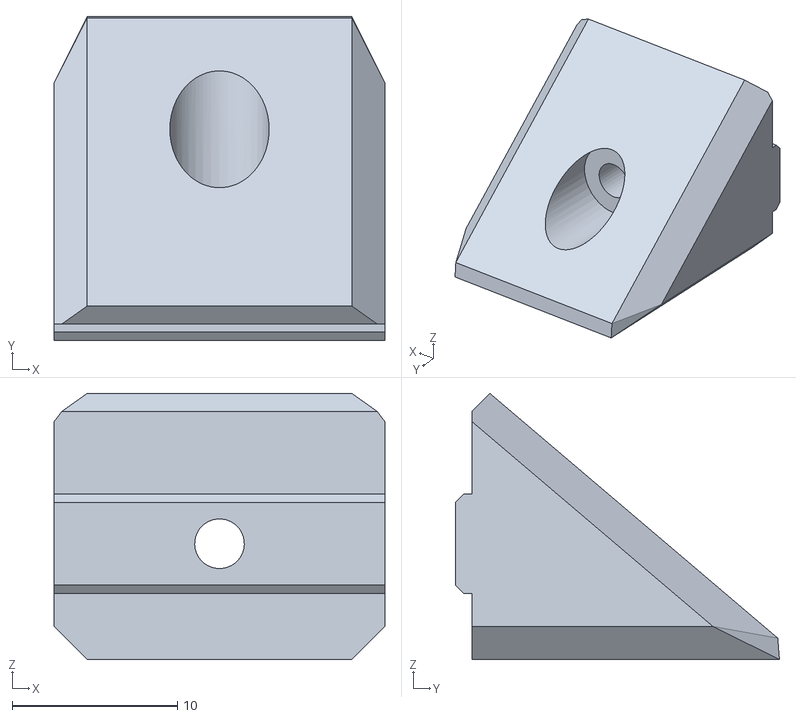
[picture p79: CAD file, 2021-03-21]
usermods/Xile_Mods/Panel Mounting/Panel_Holder_1.STL
20.0 x 19.6 x 16.1
