keithstrachan/Tiny-M/STLs/essentials/Gantry/X_Axis/X_Carriage/mini_AB_parts/printed_parts_MGN12_v4 - mini_ab - guidler.stl

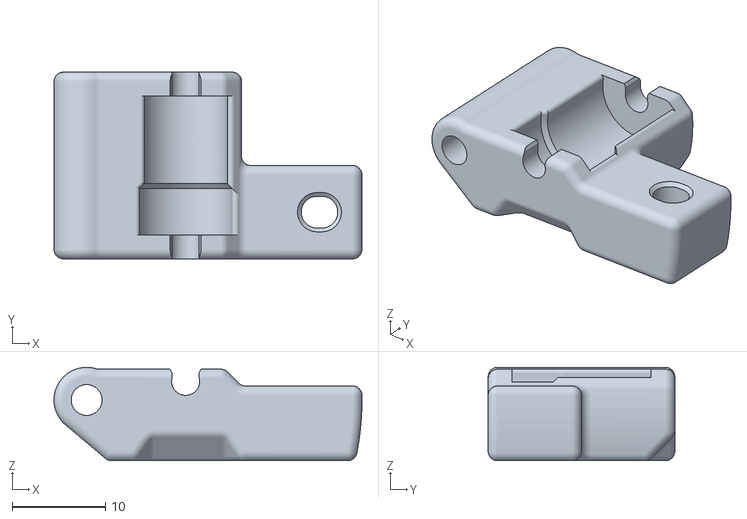
[picture p80: CAD file, 2021-05-06]
STLs/essentials/Gantry/X_Axis/X_Carriage/mini_AB_parts/printed_parts_MGN12_v4 - mini_ab - guidler.stl
33.0 x 20.0 x 10.00
