keithstrachan/Tiny-M/usermods/2020_Hinged_TopHat_Print/2020_Hinged_TopHat_Print_Front Mid Lower Print.stl

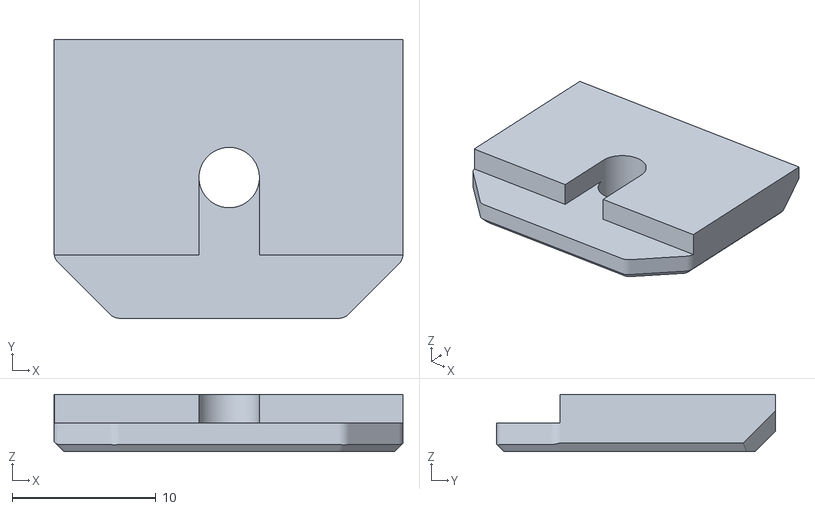
[picture p81: CAD file, 2021-03-21]
usermods/2020_Hinged_TopHat_Print/2020_Hinged_TopHat_Print_Front Mid Lower Print.stl
24.3 x 19.4 x 4.00
