keithstrachan/Tiny-M/usermods/all_metal_bed_undercarriage/CAD/150_bed.step

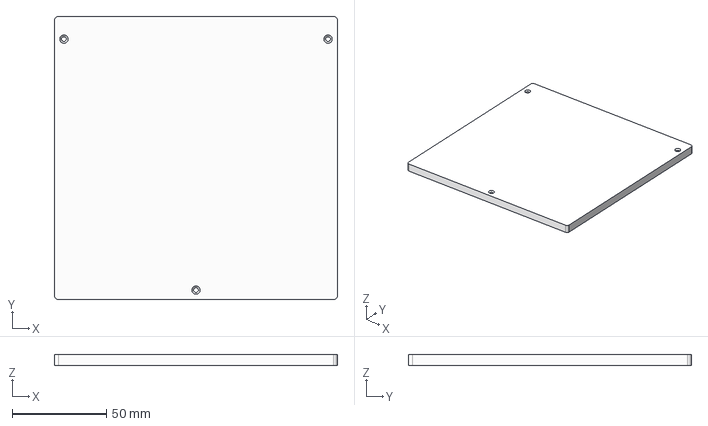
[picture p83: CAD file, 2021-05-21]
usermods/all_metal_bed_undercarriage/CAD/150_bed.step
150.0 x 150.0 x 6.00 mm
