keithstrachan/Tiny-M/usermods/all_metal_bed_undercarriage/STL/Left_End_Cap.stl

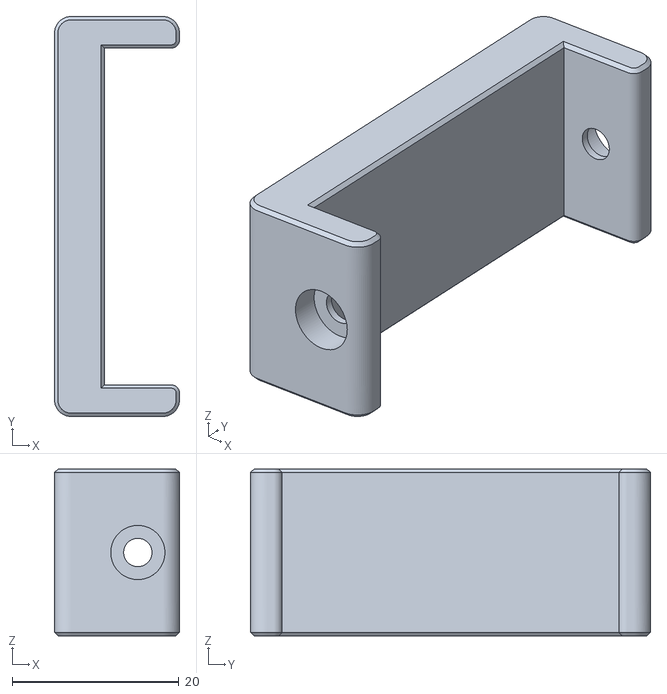
[picture p84: CAD file, 2021-05-21]
usermods/all_metal_bed_undercarriage/STL/Left_End_Cap.stl
15.0 x 48.0 x 20.0
