keithstrachan/Tiny-M/usermods/almost_all_metal_undercarriage_with_purge_bucket/STLs/bed_leadcrew_mount.3mf

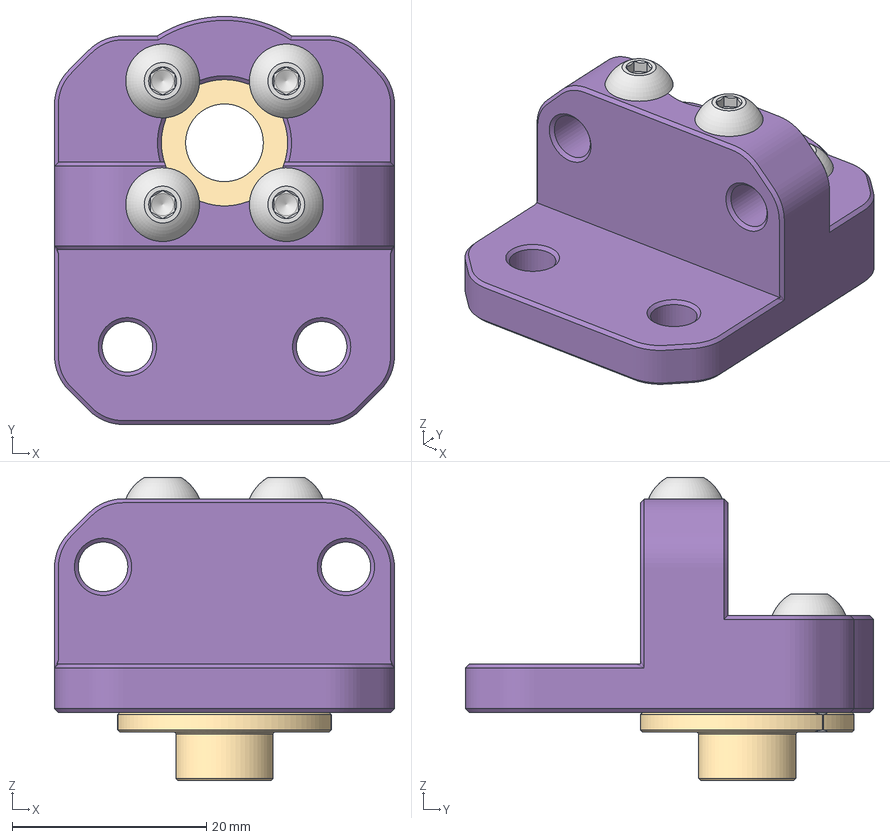
[picture p85: CAD file, 2021-12-28]
usermods/almost_all_metal_undercarriage_with_purge_bucket/STLs/bed_leadcrew_mount.3mf
35.0 x 42.0 x 31.2 mm
bed_leadcrew_mount
