keithstrachan/Tiny-M/usermods/belted_z_mod/STLs/Z Belt Top Clip.stl

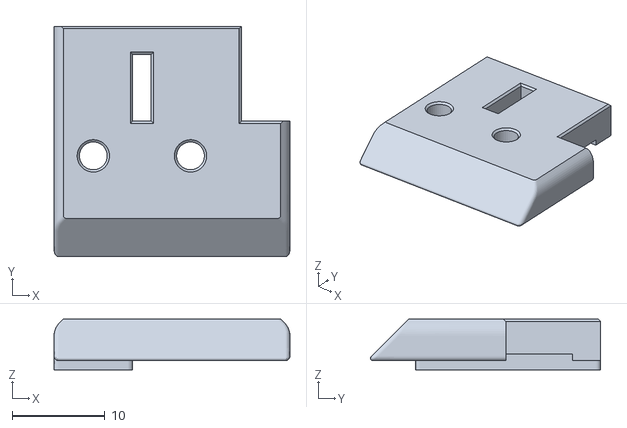
[picture p86: CAD file, 2021-05-12]
usermods/belted_z_mod/STLs/Z Belt Top Clip.stl
25.5 x 24.9 x 5.50
