keithstrachan/Tiny-M/usermods/door_handle/stl/Door_Latch.stl

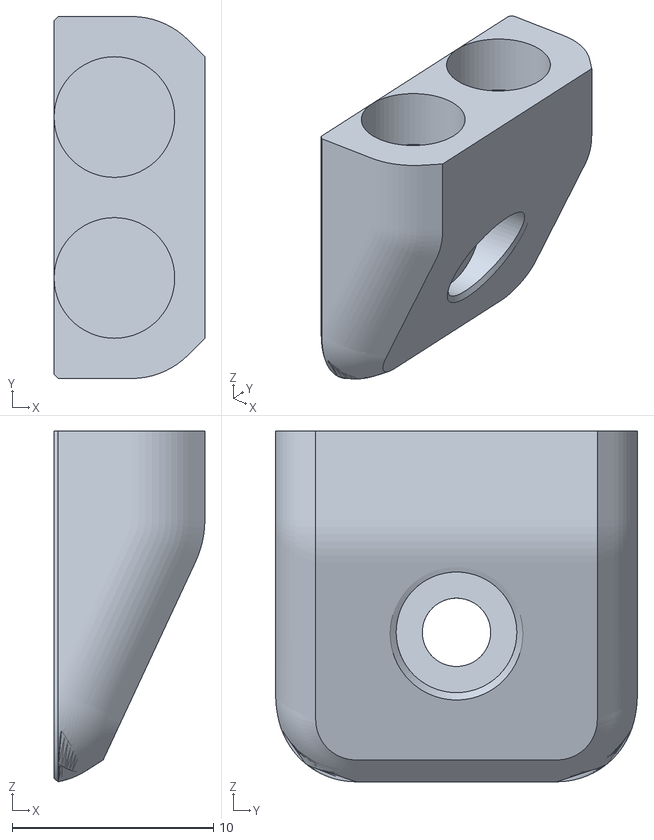
[picture p87: CAD file, 2022-09-30]
usermods/door_handle/stl/Door_Latch.stl
7.50 x 18.0 x 17.4
