keithstrachan/Tiny-M/usermods/high_torque_belted_z/STLs/150mm ver/idlerm5p1.stl

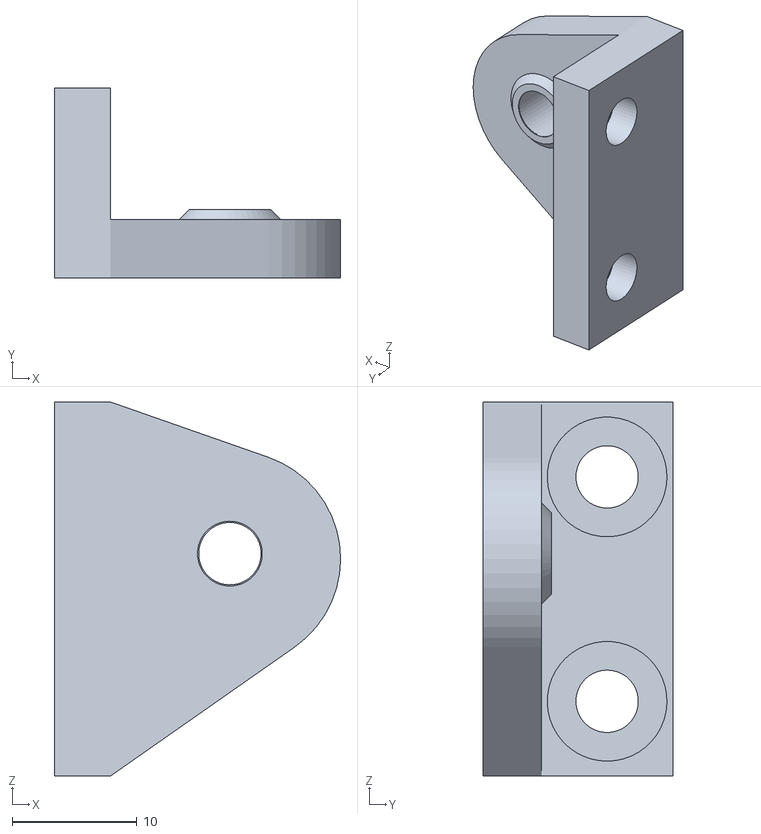
[picture p88: CAD file, 2021-12-28]
usermods/high_torque_belted_z/STLs/150mm ver/idlerm5p1.stl
23.0 x 15.3 x 30.0
