keithstrachan/Tiny-M/usermods/high_torque_belted_z/STLs/tensioner_back_plate.stl

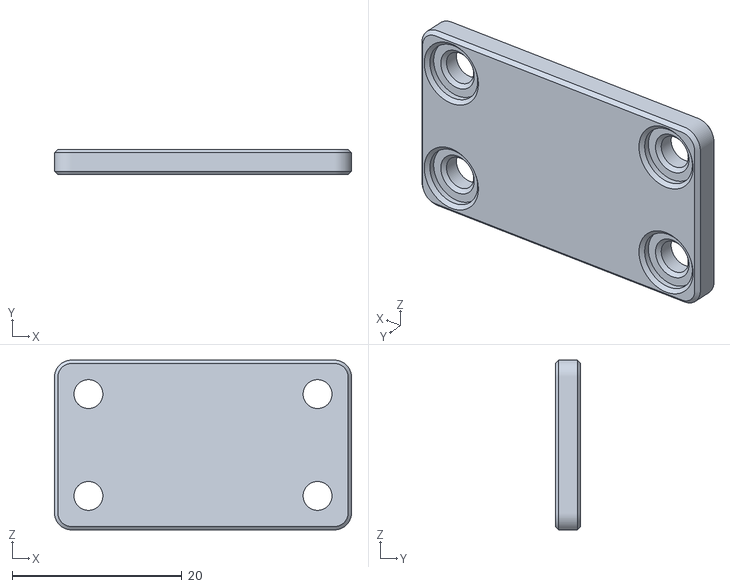
[picture p89: CAD file, 2021-09-06]
usermods/high_torque_belted_z/STLs/tensioner_back_plate.stl
35.0 x 3.00 x 20.0
