keithstrachan/Tiny-M/usermods/mgn12_x_rail/Tiny-M_Gantry_Belt_Parts.stl

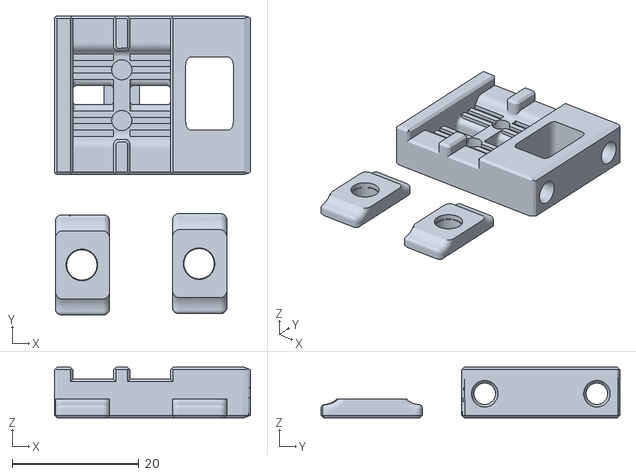
[picture p90: CAD file, 2021-03-21]
usermods/mgn12_x_rail/Tiny-M_Gantry_Belt_Parts.stl
31.0 x 47.2 x 8.00
