keithstrachan/Tiny-M/usermods/triple_z_belted/STL/idler_mount_x3.stl

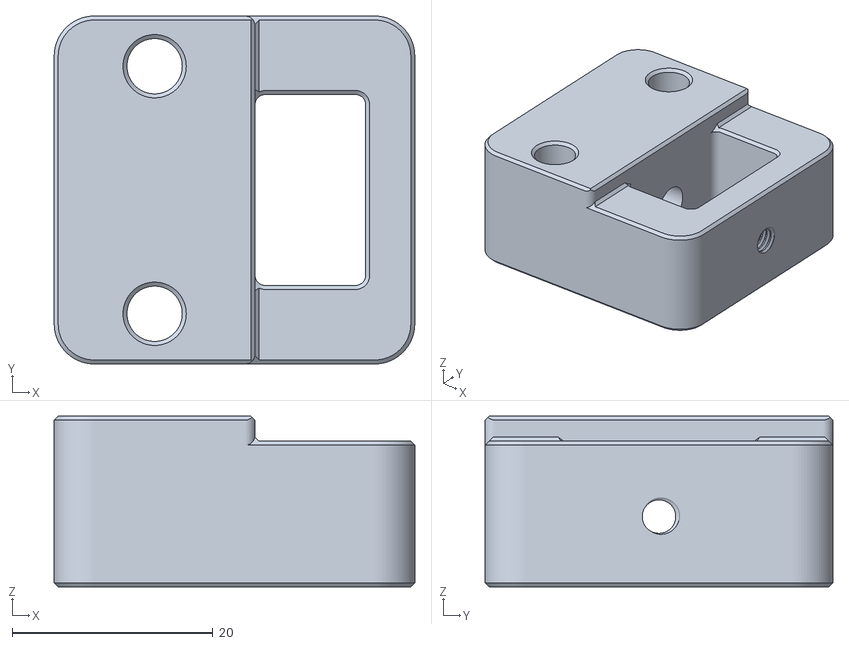
[picture p91: CAD file, 2021-05-16]
usermods/triple_z_belted/STL/idler_mount_x3.stl
35.9 x 34.6 x 17.0
