keithstrachan/Tiny-M/STLs/essentials/Gantry/X_Axis/X_Carriage/mini_AB_parts/printed_parts_MGN12_v4 - mini_ab - logo_tm.stl

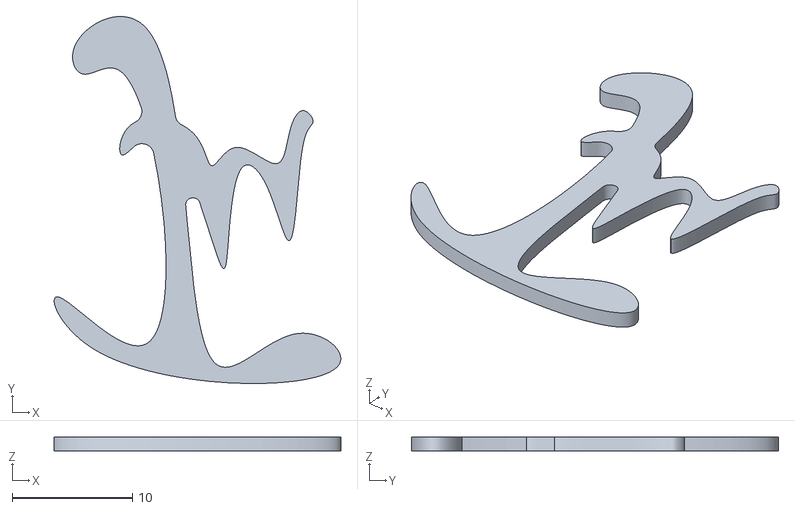
[picture p92: CAD file, 2021-05-06]
STLs/essentials/Gantry/X_Axis/X_Carriage/mini_AB_parts/printed_parts_MGN12_v4 - mini_ab - logo_tm.stl
23.9 x 30.6 x 1.20
