keithstrachan/Tiny-M/usermods/2020_Hinged_TopHat_Print/2020_Hinged_TopHat_Print_Alignment Foot 2 Print.stl

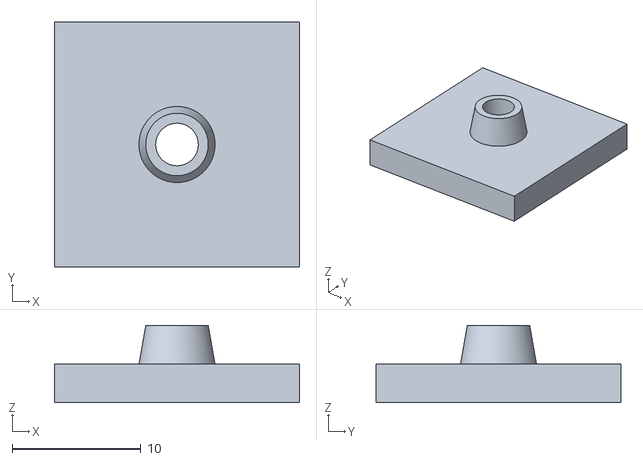
[picture p93: CAD file, 2021-03-21]
usermods/2020_Hinged_TopHat_Print/2020_Hinged_TopHat_Print_Alignment Foot 2 Print.stl
19.0 x 19.0 x 6.00
