keithstrachan/Tiny-M/usermods/5mm_idler_pins/STL/a_drive_left_top_V4.stl

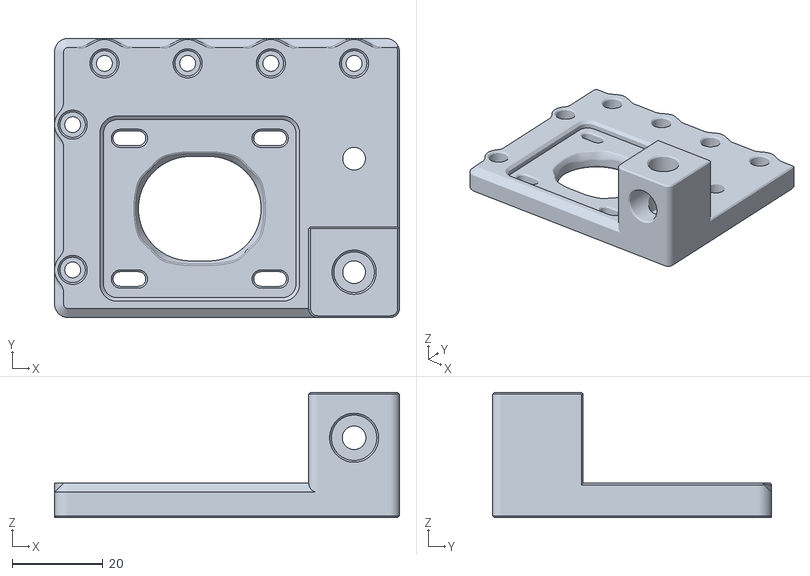
[picture p95: CAD file, 2021-03-31]
usermods/5mm_idler_pins/STL/a_drive_left_top_V4.stl
76.0 x 61.5 x 27.6
