keithstrachan/Tiny-M/usermods/all_metal_bed_undercarriage/CAD/190mm.step

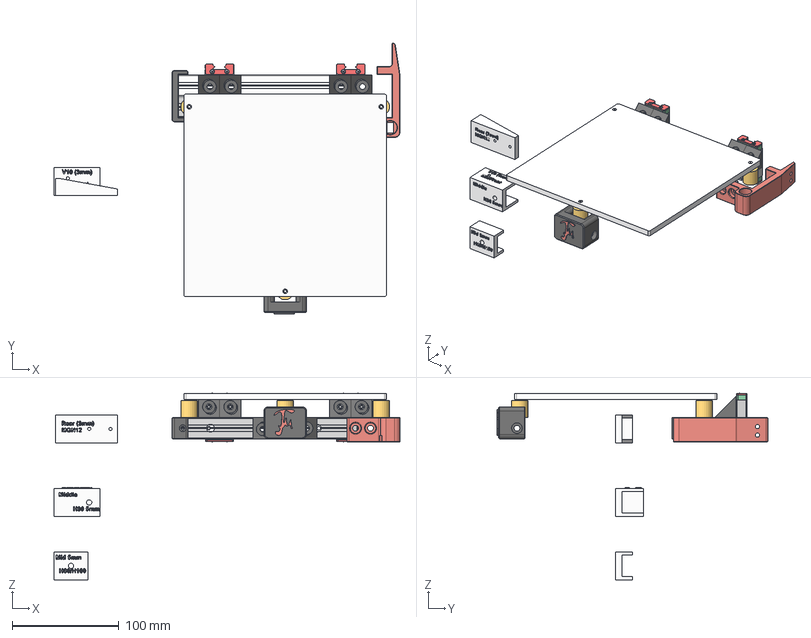
[picture p96: CAD file, 2021-05-21]
usermods/all_metal_bed_undercarriage/CAD/190mm.step
324.4 x 253.7 x 175.0 mm
Bed
MGN12H, LINEAR GUIDE BLOCK x 2
Silicone Bed Spacer
End Cap
Nameplate
HFSB5-2020-160-LCV-RCV-AH30-BH80-CH130
HFSB5-2020-160-Drilled
Z Touch and Chain Mount
Jigs
