keithstrachan/Tiny-M/usermods/all_metal_bed_undercarriage/STL/middle_front_drill_jig.stl

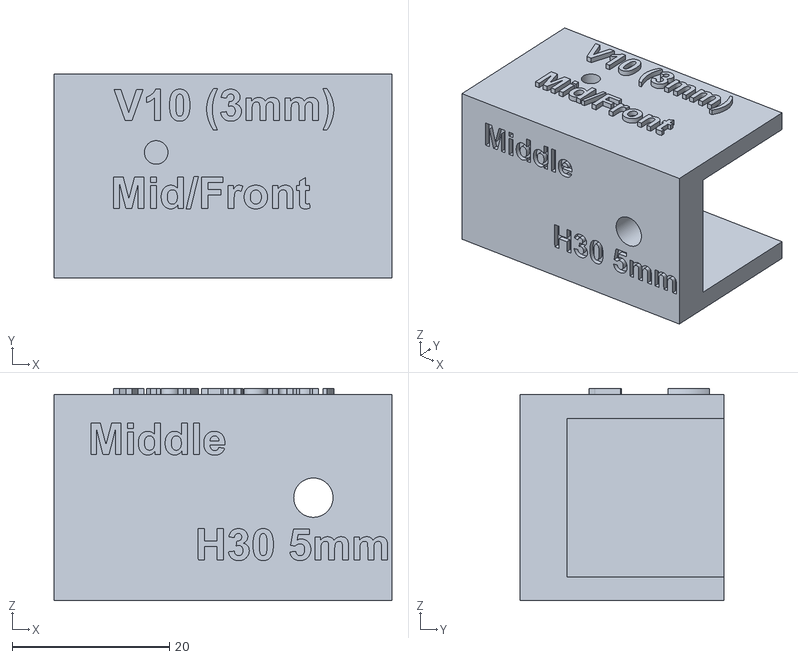
[picture p97: CAD file, 2021-05-21]
usermods/all_metal_bed_undercarriage/STL/middle_front_drill_jig.stl
43.0 x 26.0 x 27.0
