keithstrachan/Tiny-M/usermods/belted_z_mod/STLs/Z Belt Bottom Clip.stl

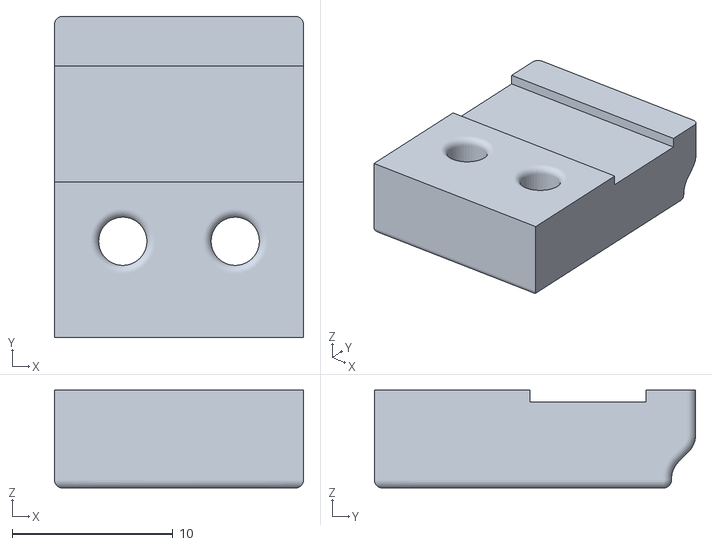
[picture p98: CAD file, 2021-05-12]
usermods/belted_z_mod/STLs/Z Belt Bottom Clip.stl
15.5 x 20.0 x 6.10
