keithstrachan/Tiny-M/usermods/high_torque_belted_z/STLs/[a]_shaft_guide.stl

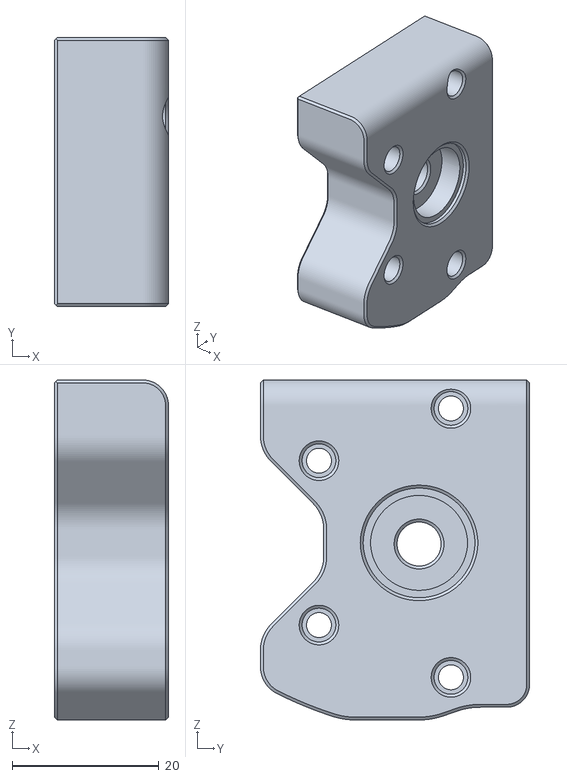
[picture p99: CAD file, 2021-09-06]
usermods/high_torque_belted_z/STLs/[a]_shaft_guide.stl
15.5 x 36.7 x 46.4
