keithstrachan/Tiny-M/STLs/essentials/Gantry/X_Axis/X_Carriage/mini_AB_parts/printed_parts_MGN12_v4 - bw_dd_sch_wing_mini_ab.stl

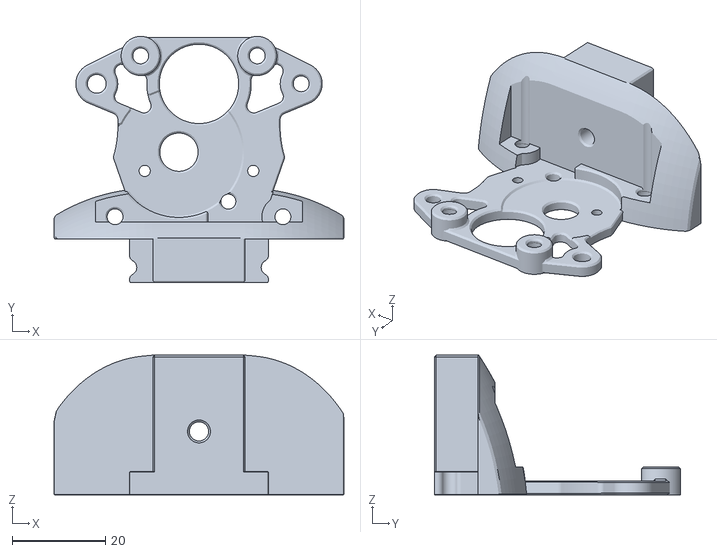
[picture p100: CAD file, 2021-05-06]
STLs/essentials/Gantry/X_Axis/X_Carriage/mini_AB_parts/printed_parts_MGN12_v4 - bw_dd_sch_wing_mini_ab.stl
62.2 x 52.8 x 30.0
