keithstrachan/Tiny-M/STLs/essentials/Gantry/X_Axis/X_Carriage/printed_parts_MGN12_v4 - bw_dd_sch_wing_sailfin.stl

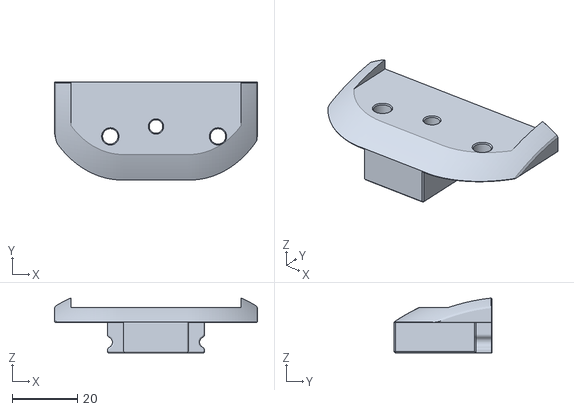
[picture p101: CAD file, 2021-03-31]
STLs/essentials/Gantry/X_Axis/X_Carriage/printed_parts_MGN12_v4 - bw_dd_sch_wing_sailfin.stl
62.2 x 30.0 x 16.8
