keithstrachan/Tiny-M/usermods/2020_Hinged_TopHat_Print/2020_Hinged_TopHat_Print_Front Left Upper Print.stl

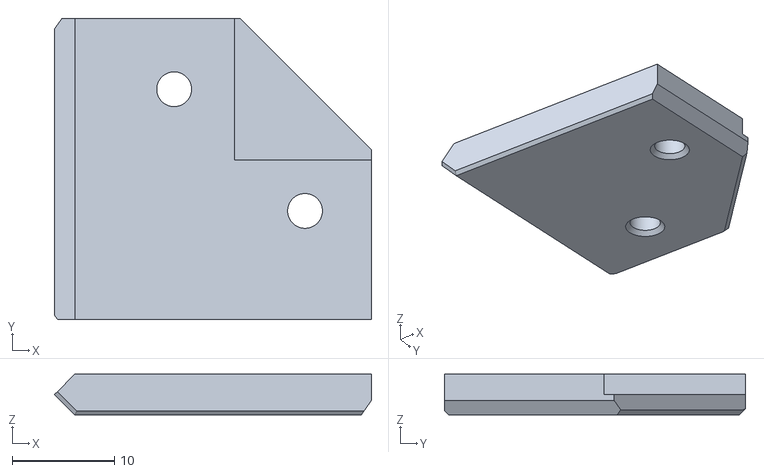
[picture p102: CAD file, 2021-03-21]
usermods/2020_Hinged_TopHat_Print/2020_Hinged_TopHat_Print_Front Left Upper Print.stl
31.0 x 29.4 x 4.00
