keithstrachan/Tiny-M/usermods/5mm_idler_pins/CAD/ab_drive_unit_left_v4_5mm_Pin v4.step

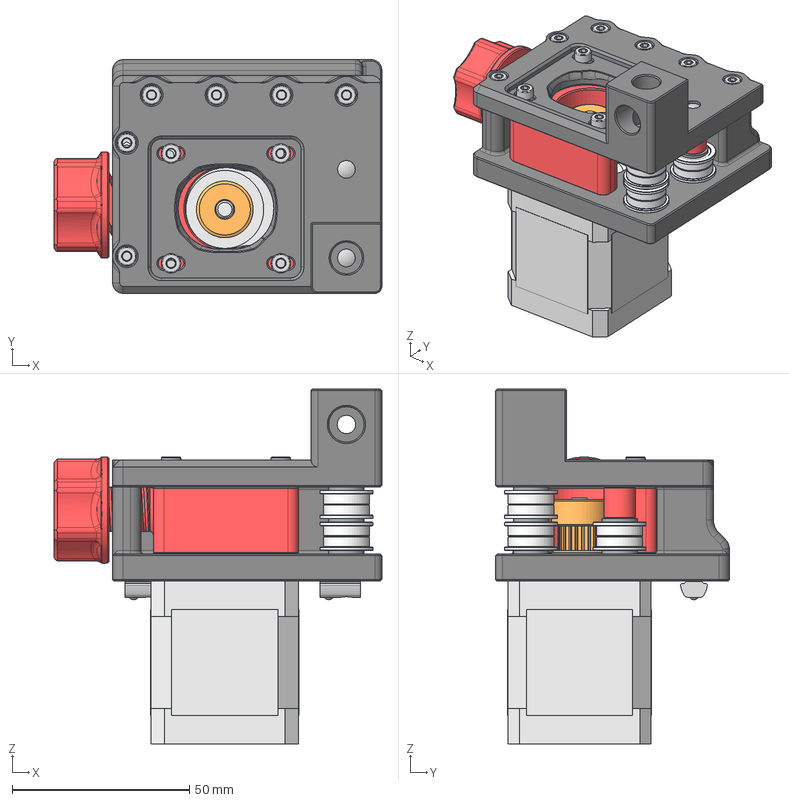
[picture p103: CAD file, 2021-03-31]
usermods/5mm_idler_pins/CAD/ab_drive_unit_left_v4_5mm_Pin v4.step
92.5 x 66.0 x 100.2 mm
F695-2RS x 6
DIN 934 M3 x 2
DIN 988 5x10x1 Shim Ring x 5
DIN 912 M3x35 x 8
a_drive_left_bottom_V4
GT2_20T
M3-T-Nut x 4
DIN 912 M3x30 x 2
Motor 17HS19-2004S
[a]_ab_drive_spacer_9mm
[a]_a_drive_left_tensioner_V4
[a]_a_drive_knop_V4
a_drive_left_top_V4
91595A376_32mm_METRIC ALLOY STEEL DOWEL PIN x 2
