keithstrachan/Tiny-M/usermods/all_metal_bed_undercarriage/STL/MGN12_drill_jig.stl

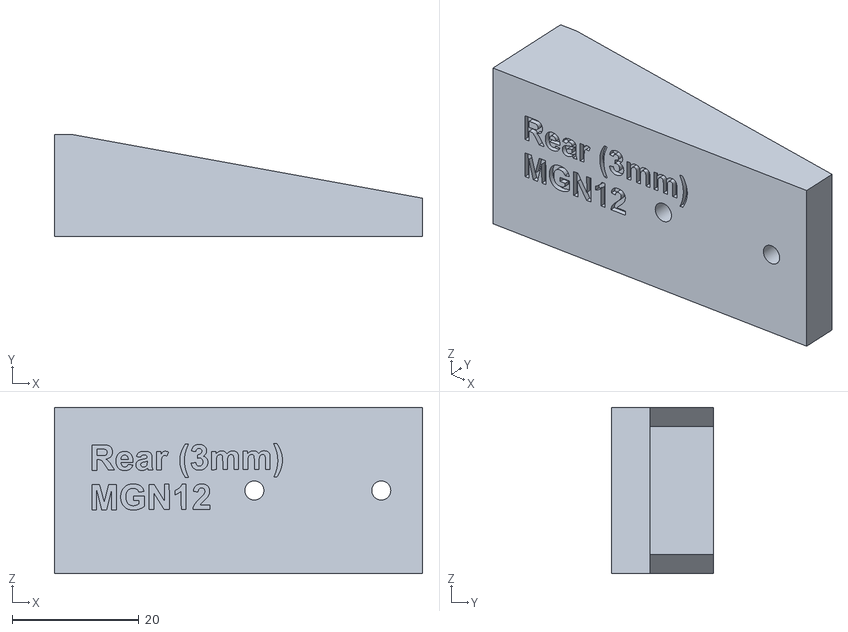
[picture p104: CAD file, 2021-05-21]
usermods/all_metal_bed_undercarriage/STL/MGN12_drill_jig.stl
58.0 x 16.0 x 26.2
