keithstrachan/Tiny-M/usermods/almost_all_metal_undercarriage_with_purge_bucket/STLs/bed_left_mount.3mf

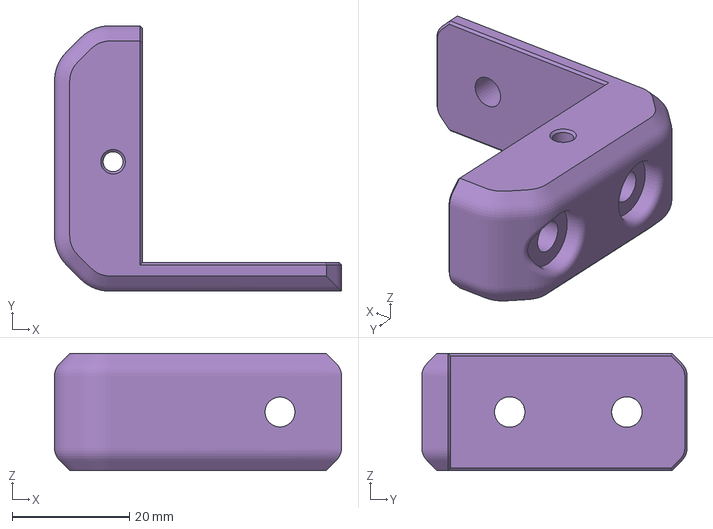
[picture p105: CAD file, 2021-12-28]
usermods/almost_all_metal_undercarriage_with_purge_bucket/STLs/bed_left_mount.3mf
49.0 x 45.3 x 20.0 mm
