keithstrachan/Tiny-M/usermods/belted_z_mod/STLs/Top Z Idler Large.stl

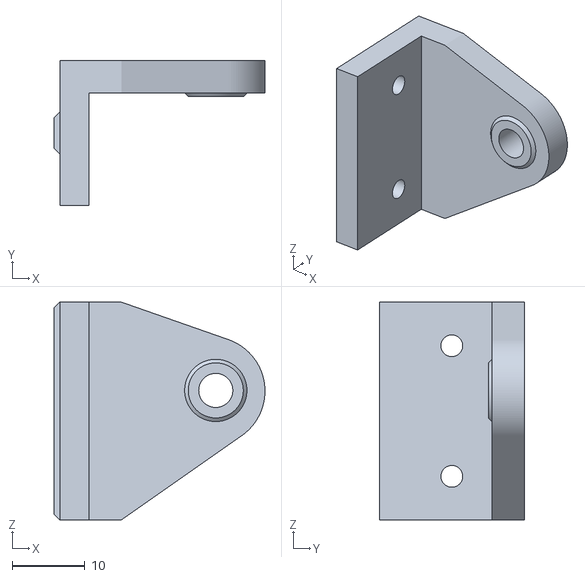
[picture p106: CAD file, 2021-05-12]
usermods/belted_z_mod/STLs/Top Z Idler Large.stl
29.1 x 20.0 x 30.0
