keithstrachan/Tiny-M/usermods/high_torque_belted_z/STLs/tensioner.stl

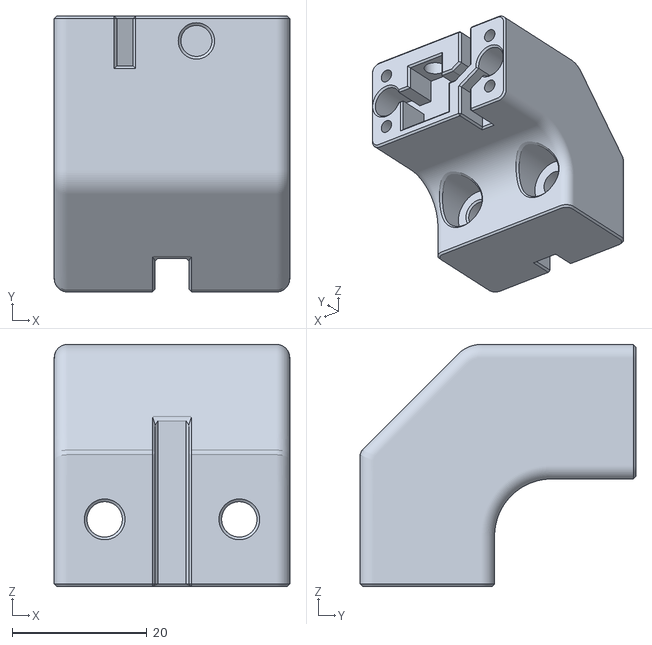
[picture p107: CAD file, 2021-09-06]
usermods/high_torque_belted_z/STLs/tensioner.stl
35.0 x 41.0 x 36.0
