keithstrachan/Tiny-M/usermods/triple_z_belted/STL/maxwell_x3.stl

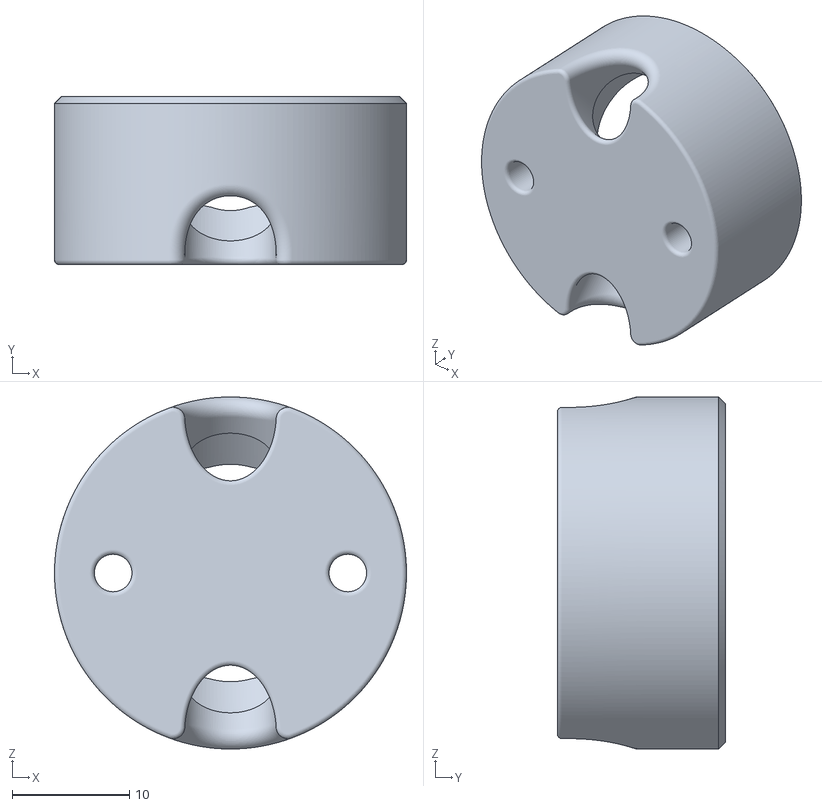
[picture p108: CAD file, 2021-05-16]
usermods/triple_z_belted/STL/maxwell_x3.stl
30.0 x 14.3 x 30.0
