keithstrachan/Tiny-M/STLs/essentials/Gantry/X_Axis/X_Carriage/mini_AB_parts/printed_parts_MGN12_v4 - mini_ab - latch.stl

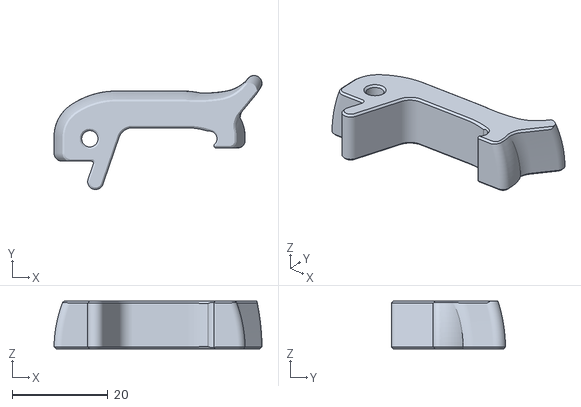
[picture p109: CAD file, 2021-05-06]
STLs/essentials/Gantry/X_Axis/X_Carriage/mini_AB_parts/printed_parts_MGN12_v4 - mini_ab - latch.stl
43.5 x 23.9 x 10.0
