keithstrachan/Tiny-M/STLs/essentials/Gantry/X_Axis/X_Carriage/printed_parts_MGN12_v4 - bw_dd_sch_fan_duct_left.stl

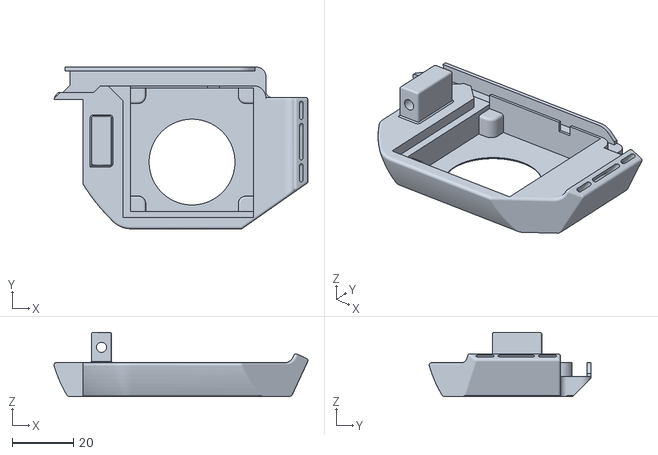
[picture p110: CAD file, 2021-03-24]
STLs/essentials/Gantry/X_Axis/X_Carriage/printed_parts_MGN12_v4 - bw_dd_sch_fan_duct_left.stl
82.9 x 52.8 x 21.0
