keithstrachan/Tiny-M/usermods/190mm_prusa_mini_mod/STLs/[a]_front_skirt_right.stl

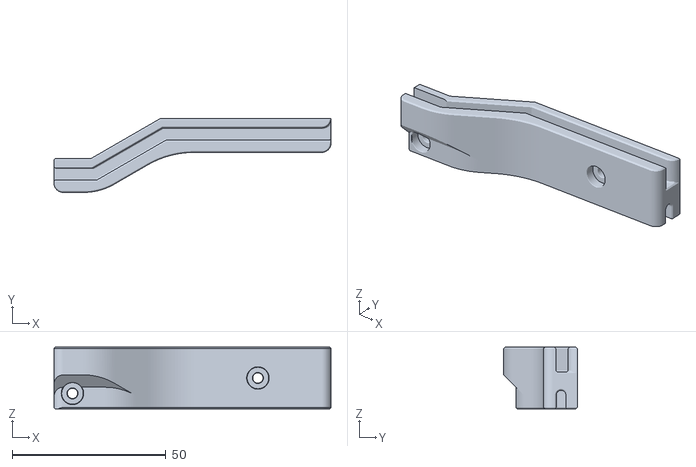
[picture p111: CAD file, 2021-04-13]
usermods/190mm_prusa_mini_mod/STLs/[a]_front_skirt_right.stl
90.0 x 24.0 x 20.0
