keithstrachan/Tiny-M/usermods/2020_Hinged_TopHat_Print/2020_Hinged_TopHat_Print_Hinge Base 2 Print.stl

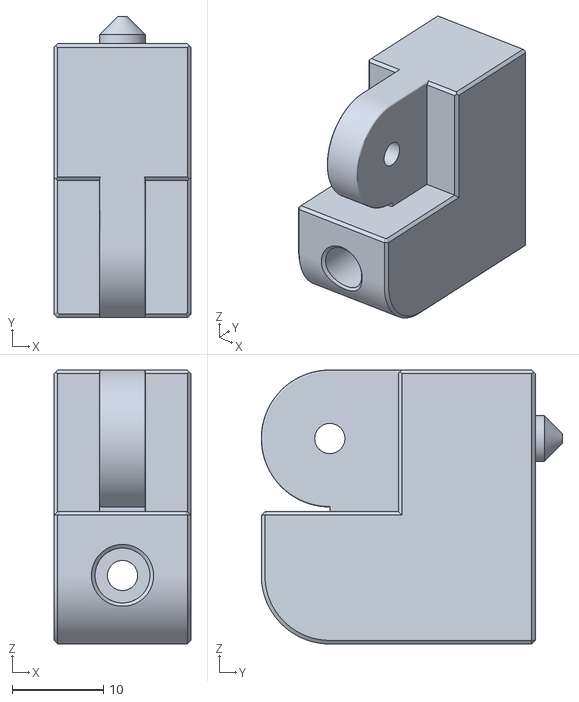
[picture p112: CAD file, 2021-03-21]
usermods/2020_Hinged_TopHat_Print/2020_Hinged_TopHat_Print_Hinge Base 2 Print.stl
15.0 x 33.0 x 30.0
