keithstrachan/Tiny-M/usermods/5mm_idler_pins/CAD/xy_joint_V4_5mm_pin v2.step

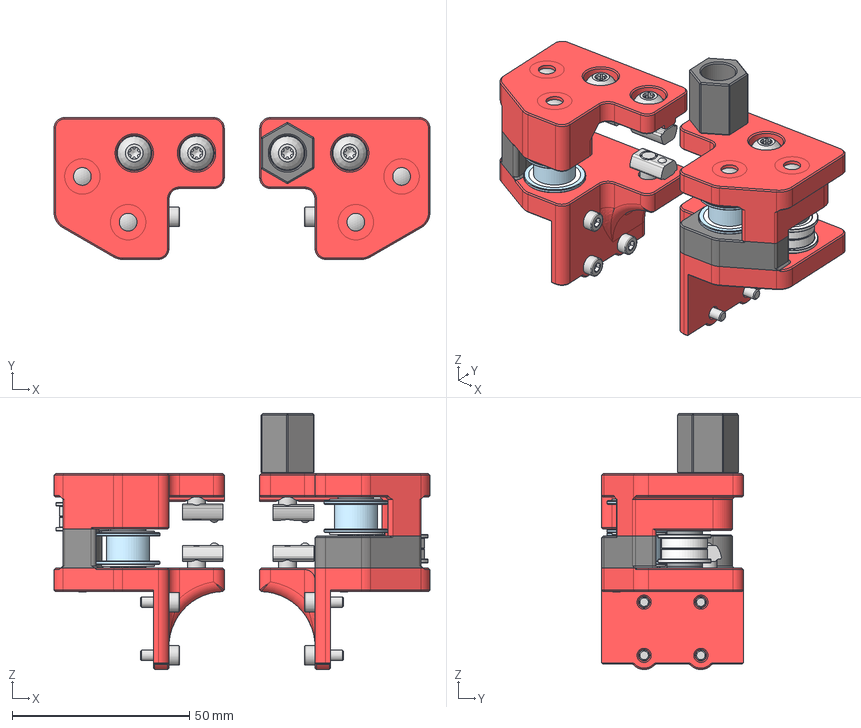
[picture p113: CAD file, 2021-03-31]
usermods/5mm_idler_pins/CAD/xy_joint_V4_5mm_pin v2.step
106.0 x 40.0 x 72.2 mm
M2x12 self tapping screw for plastic x 2
xy-join_left_top_v4_not_nut
xy-join_left_bottom_v4_not_nut
ISO 7380-1 M5x10 x 5
M5-T-Nut x 6
DIN 912 M3x8 x 8
F695-2RS x 4
DIN 912 M3x20 x 2
DIN 988 5x10x1 Shim Ring x 8
DIN 988 5x10x0.5 Shim Ring x 6
xy-join_left_middle_v4_not_nut
2GT 6MM Toothed Idler v1 x 2
Powge - 2GT-20T-idler x 2
91595A376_32mm_METRIC ALLOY STEEL DOWEL PIN x 4
xy-join_right_bottom_v4_not_nut
xy-join_endstop_block_v4
M5x20
xy-join_right_top_v4_not_nut
xy-join_right_middle_v4_not_nut
