keithstrachan/Tiny-M/usermods/5mm_idler_pins/STL/front_idler_right_bottom_V4.stl

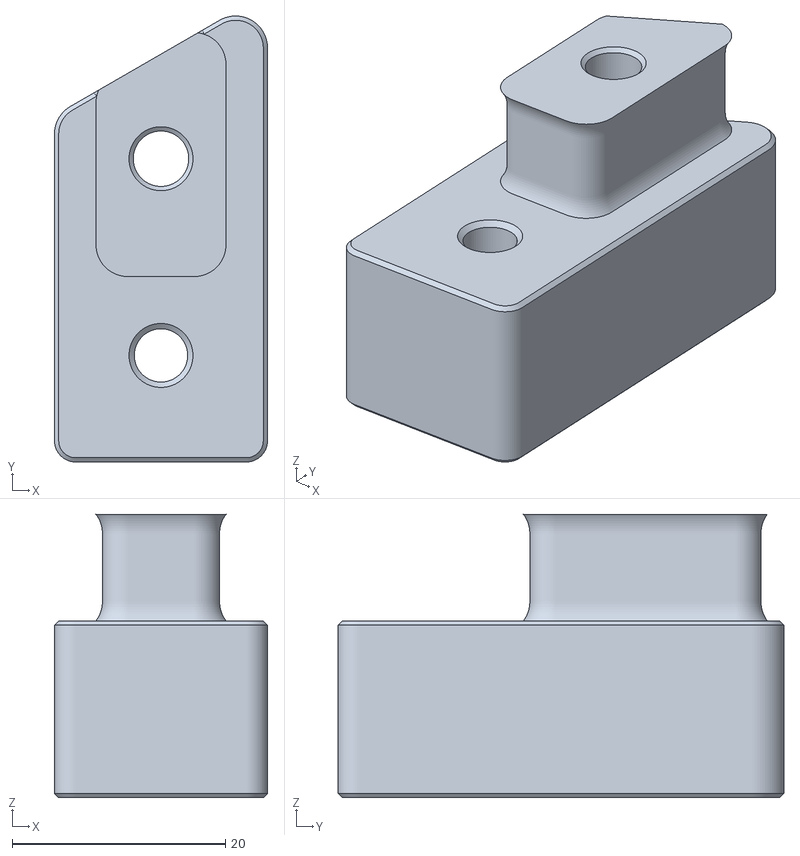
[picture p114: CAD file, 2021-03-31]
usermods/5mm_idler_pins/STL/front_idler_right_bottom_V4.stl
20.0 x 41.9 x 26.6
