keithstrachan/Tiny-M/usermods/all_metal_bed_undercarriage/STL/Nosepiece.stl

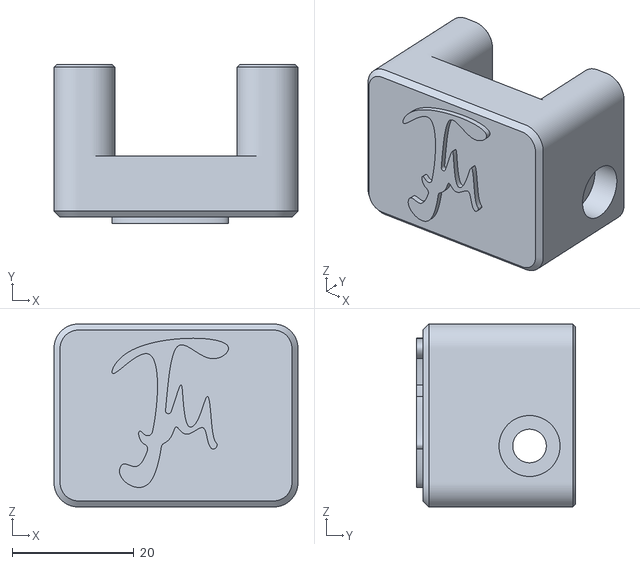
[picture p115: CAD file, 2021-05-06]
usermods/all_metal_bed_undercarriage/STL/Nosepiece.stl
40.0 x 26.0 x 30.0
