keithstrachan/Tiny-M/usermods/almost_all_metal_undercarriage_with_purge_bucket/STLs/bed_front_mount.3mf

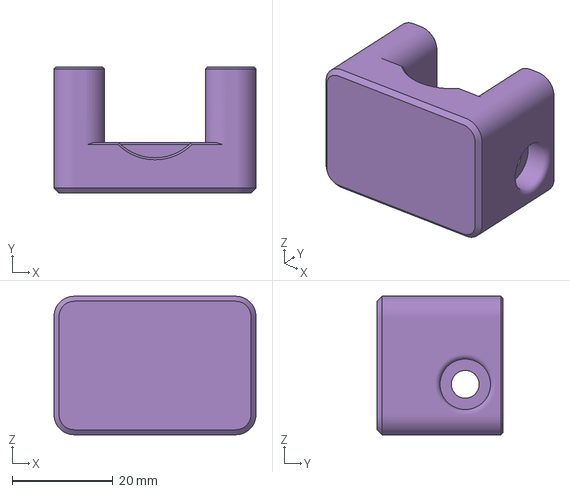
[picture p116: CAD file, 2021-12-28]
usermods/almost_all_metal_undercarriage_with_purge_bucket/STLs/bed_front_mount.3mf
40.0 x 25.0 x 27.5 mm
