keithstrachan/Tiny-M/usermods/belted_z_mod/STLs/Bottom Frame Bracket 190.stl

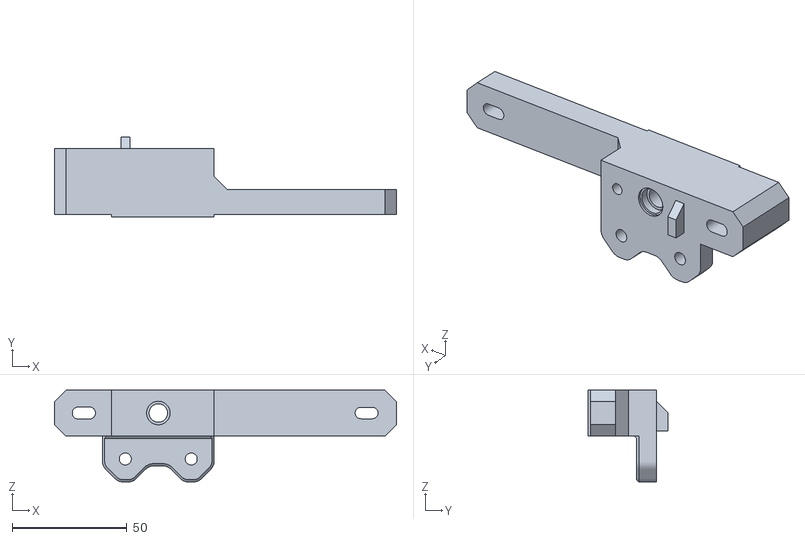
[picture p117: CAD file, 2021-05-12]
usermods/belted_z_mod/STLs/Bottom Frame Bracket 190.stl
148.8 x 34.7 x 40.0
