keithstrachan/Tiny-M/usermods/high_torque_belted_z/STLs/base_motor_plate.stl

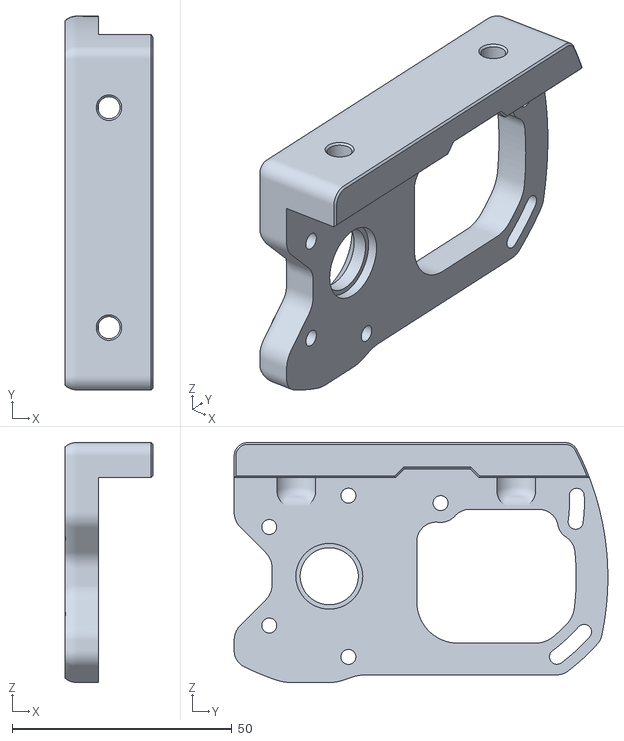
[picture p118: CAD file, 2021-09-06]
usermods/high_torque_belted_z/STLs/base_motor_plate.stl
20.0 x 85.0 x 54.6
