keithstrachan/Tiny-M/STLs/essentials/Gantry/X_Axis/X_Carriage/printed_parts_MGN12_v4 - bw_dd_sch_belt_retainer.stl

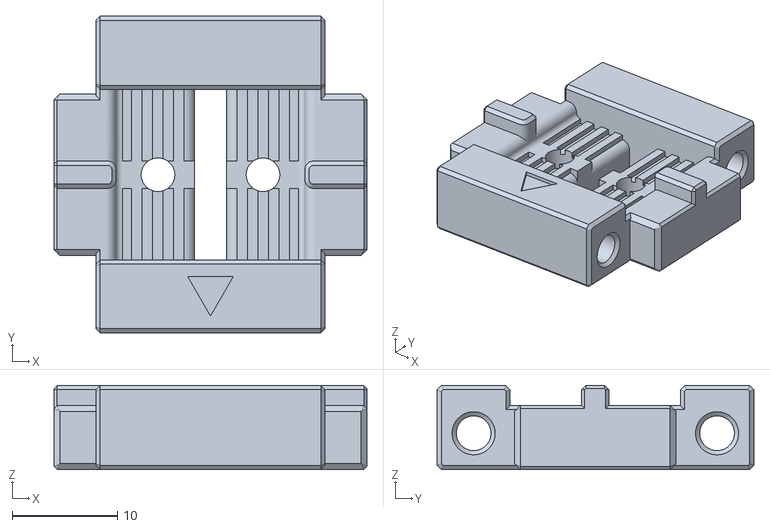
[picture p120: CAD file, 2021-03-24]
STLs/essentials/Gantry/X_Axis/X_Carriage/printed_parts_MGN12_v4 - bw_dd_sch_belt_retainer.stl
29.8 x 30.1 x 8.00
