keithstrachan/Tiny-M/usermods/190mm_prusa_mini_mod/STLs/front_skirt_right.stl

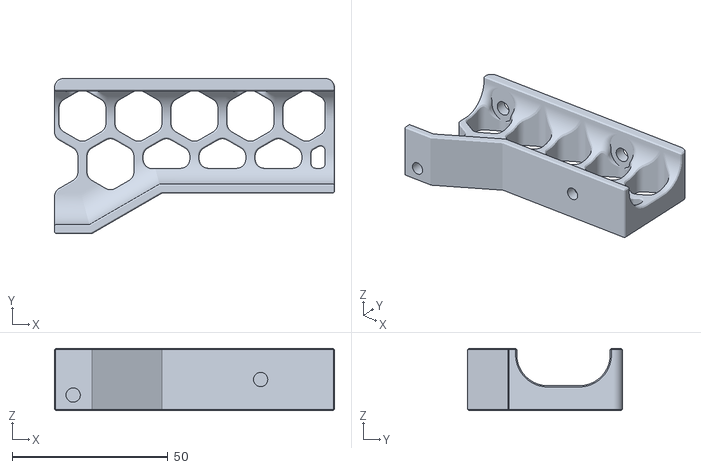
[picture p121: CAD file, 2021-04-13]
usermods/190mm_prusa_mini_mod/STLs/front_skirt_right.stl
90.0 x 49.9 x 20.0
