keithstrachan/Tiny-M/usermods/2020_Hinged_TopHat_Print/2020_Hinged_TopHat_Print_Right Lower Right Print.stl

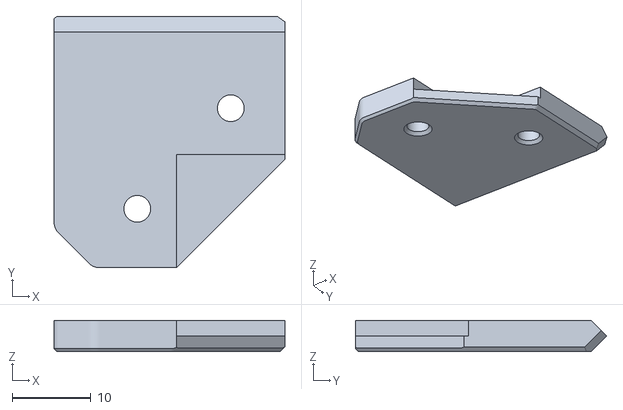
[picture p122: CAD file, 2021-03-21]
usermods/2020_Hinged_TopHat_Print/2020_Hinged_TopHat_Print_Right Lower Right Print.stl
29.4 x 32.0 x 4.00
