keithstrachan/Tiny-M/usermods/belted_z_mod/STLs/Top Z Idler Small.stl

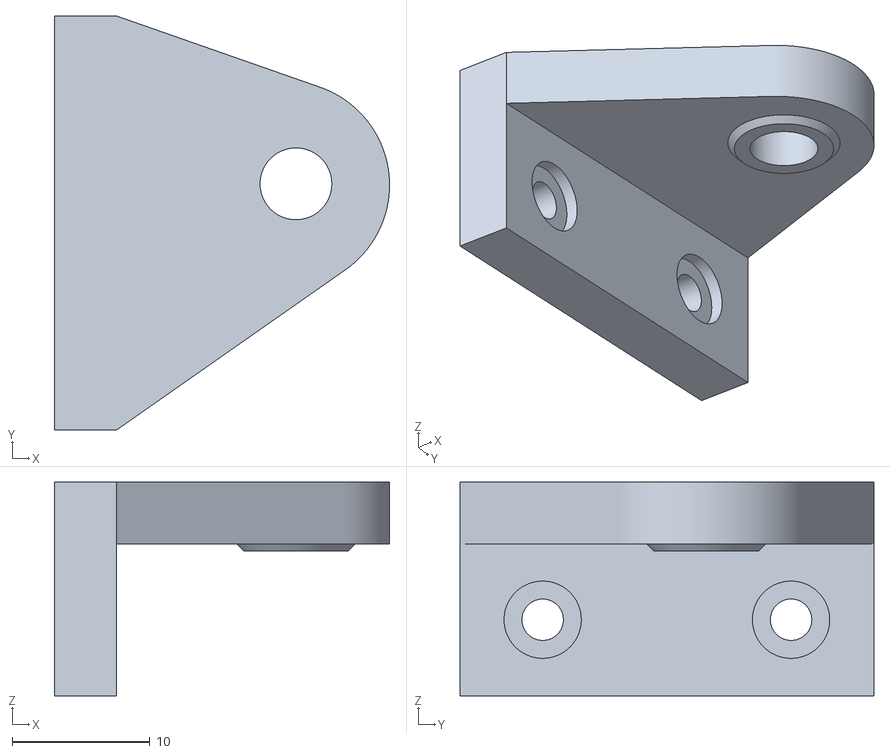
[picture p123: CAD file, 2021-05-12]
usermods/belted_z_mod/STLs/Top Z Idler Small.stl
24.3 x 30.0 x 15.5
