keithstrachan/Tiny-M/STLs/essentials/Gantry/X_Axis/X_Carriage/printed_parts_MGN12_v4 - bw_dd_sch_toolhead_dragon_right.stl

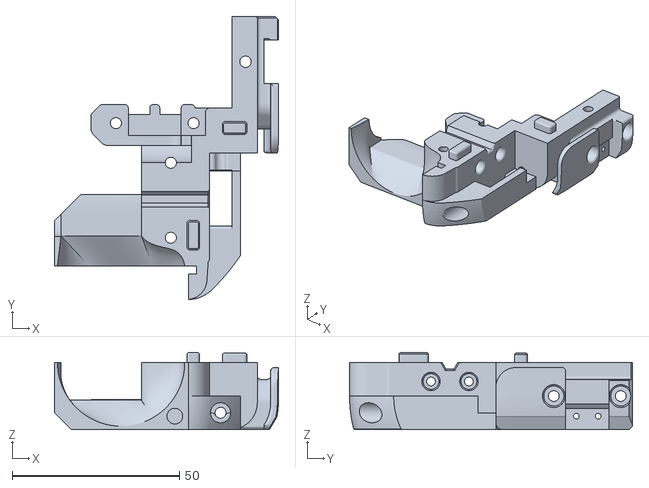
[picture p124: CAD file, 2021-03-24]
STLs/essentials/Gantry/X_Axis/X_Carriage/printed_parts_MGN12_v4 - bw_dd_sch_toolhead_dragon_right.stl
67.0 x 84.5 x 23.0
