keithstrachan/Tiny-M/usermods/5mm_idler_pins/STL/a_drive_left_bottom_V4.stl

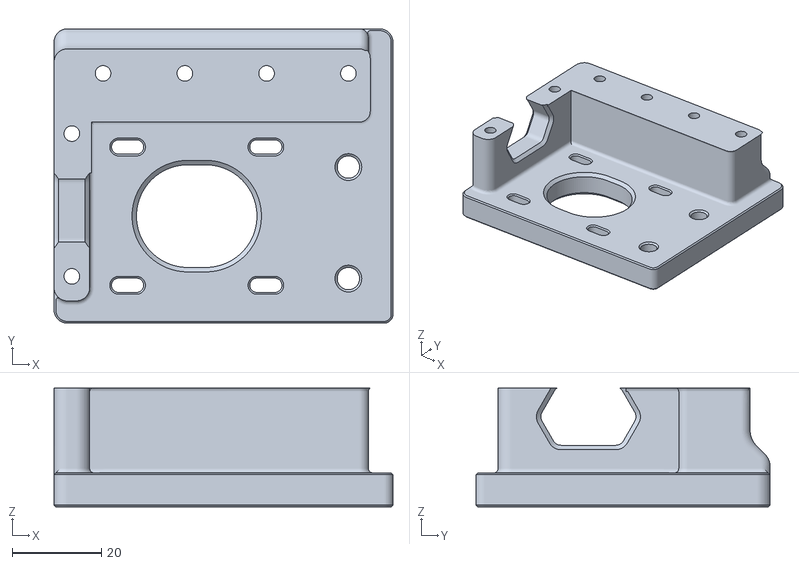
[picture p125: CAD file, 2021-03-31]
usermods/5mm_idler_pins/STL/a_drive_left_bottom_V4.stl
76.0 x 66.0 x 26.6
