keithstrachan/Tiny-M/usermods/belted_z_mod/STLs/Z Belt Bed Mount.stl

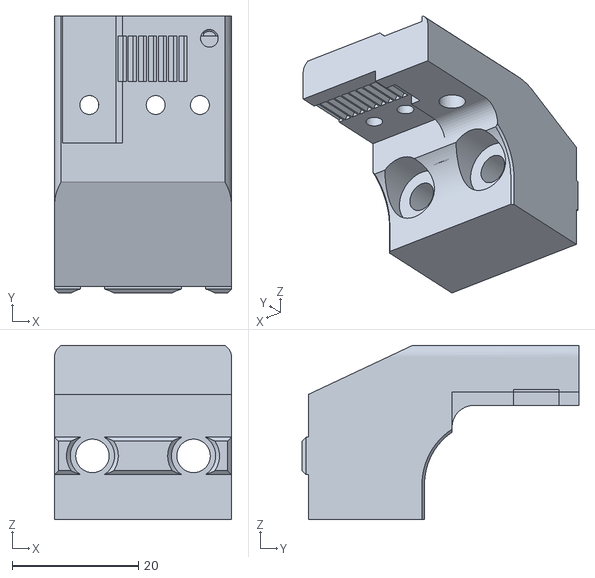
[picture p126: CAD file, 2021-05-12]
usermods/belted_z_mod/STLs/Z Belt Bed Mount.stl
28.0 x 43.8 x 27.6
