keithstrachan/Tiny-M/STLs/essentials/Gantry/X_Axis/X_Carriage/printed_parts_MGN12_v4 - bw_dd_sch_cable_plate_alpha.stl

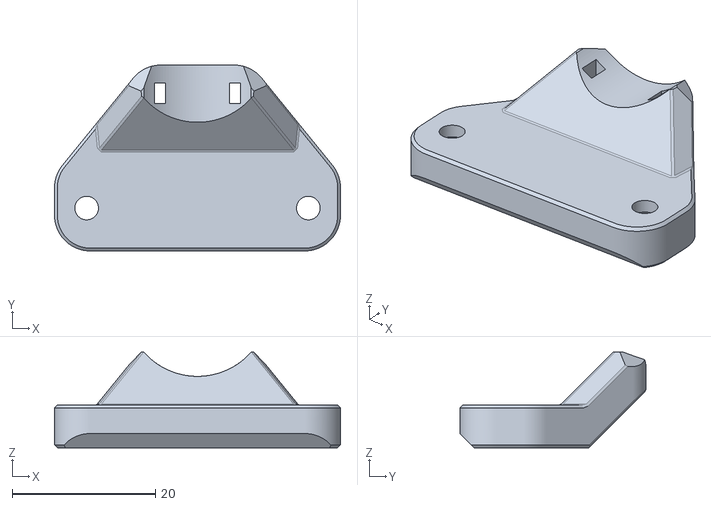
[picture p127: CAD file, 2021-03-24]
STLs/essentials/Gantry/X_Axis/X_Carriage/printed_parts_MGN12_v4 - bw_dd_sch_cable_plate_alpha.stl
40.0 x 26.0 x 13.4
