keithstrachan/Tiny-M/usermods/5mm_idler_pins/STL/front_idler_right_top_V4.stl

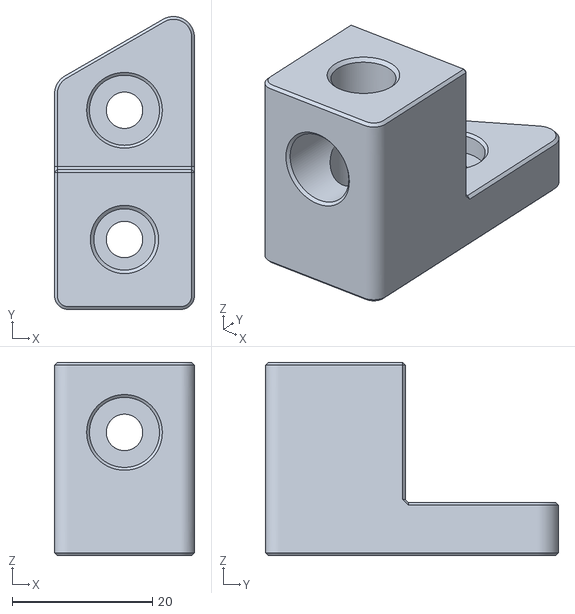
[picture p128: CAD file, 2021-03-31]
usermods/5mm_idler_pins/STL/front_idler_right_top_V4.stl
20.0 x 41.9 x 27.6
