keithstrachan/Tiny-M/usermods/190mm_prusa_mini_mod/STLs/z_positioner_upper_190_z_positioner_upper.stl

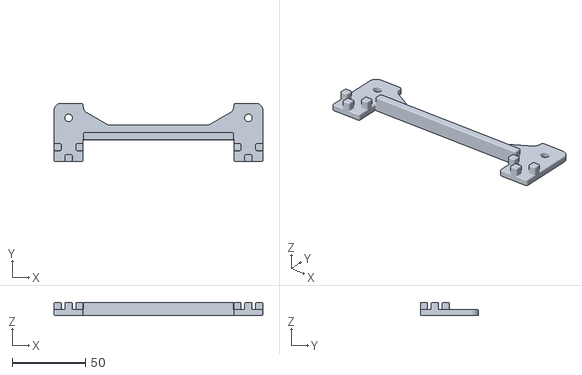
[picture p129: CAD file, 2021-03-21]
usermods/190mm_prusa_mini_mod/STLs/z_positioner_upper_190_z_positioner_upper.stl
143.0 x 40.0 x 9.00
