keithstrachan/Tiny-M/STLs/essentials/Gantry/X_Axis/X_Carriage/tools - MGN12_alignment_1mm_offset.stl

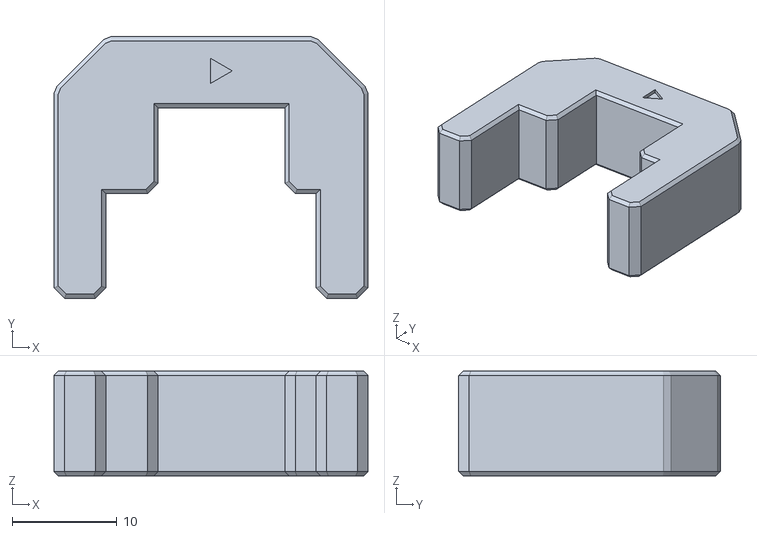
[picture p130: CAD file, 2021-03-24]
STLs/essentials/Gantry/X_Axis/X_Carriage/tools - MGN12_alignment_1mm_offset.stl
30.0 x 25.0 x 10.0
