keithstrachan/Tiny-M/usermods/190mm_prusa_mini_mod/STLs/z_positioner_lower_190_z_position_lower.stl

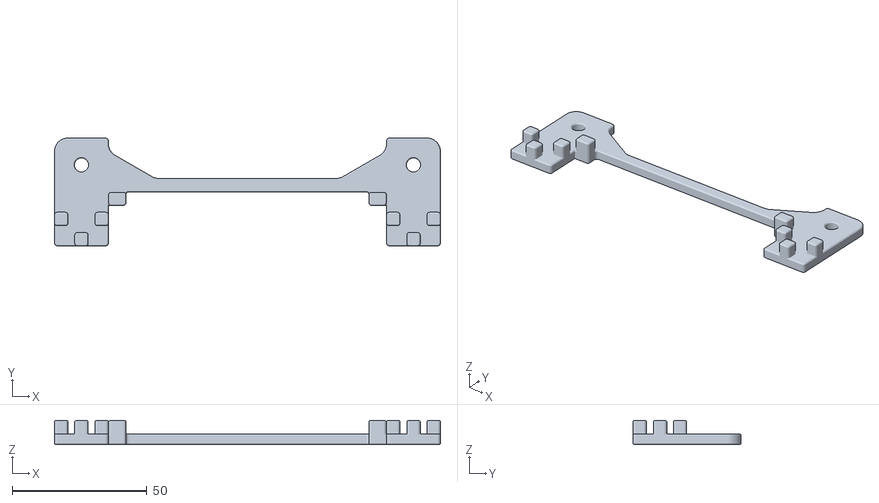
[picture p131: CAD file, 2021-03-21]
usermods/190mm_prusa_mini_mod/STLs/z_positioner_lower_190_z_position_lower.stl
143.0 x 40.0 x 9.00
