keithstrachan/Tiny-M/usermods/190mm_prusa_mini_mod/STLs/front_bed_mount_proud_text_190_front_bed_mount_proud_text.stl

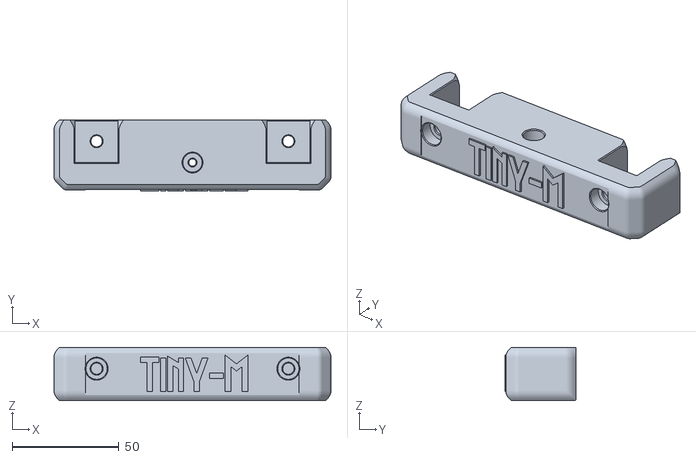
[picture p134: CAD file, 2021-03-21]
usermods/190mm_prusa_mini_mod/STLs/front_bed_mount_proud_text_190_front_bed_mount_proud_text.stl
130.0 x 33.4 x 25.0
