keithstrachan/Tiny-M/usermods/190mm_prusa_mini_mod/STLs/guide_bed_190_guide_bed_190.stl

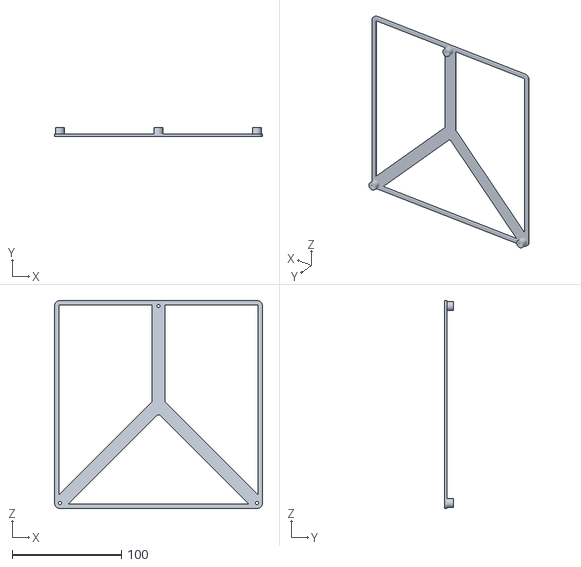
[picture p136: CAD file, 2021-03-21]
usermods/190mm_prusa_mini_mod/STLs/guide_bed_190_guide_bed_190.stl
190.0 x 8.00 x 190.0
