keithstrachan/Tiny-M/usermods/2020_Hinged_TopHat_Print/2020_Hinged_TopHat_Print_Top Mid Front Print.stl

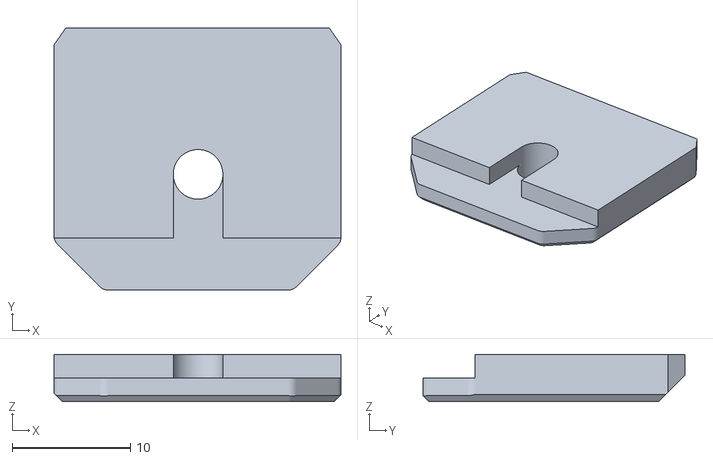
[picture p137: CAD file, 2021-03-21]
usermods/2020_Hinged_TopHat_Print/2020_Hinged_TopHat_Print_Top Mid Front Print.stl
24.3 x 22.2 x 4.00
