keithstrachan/Tiny-M/usermods/2020_Hinged_TopHat_Print/2020_Hinged_TopHat_Print_Top Rear Left Print.stl

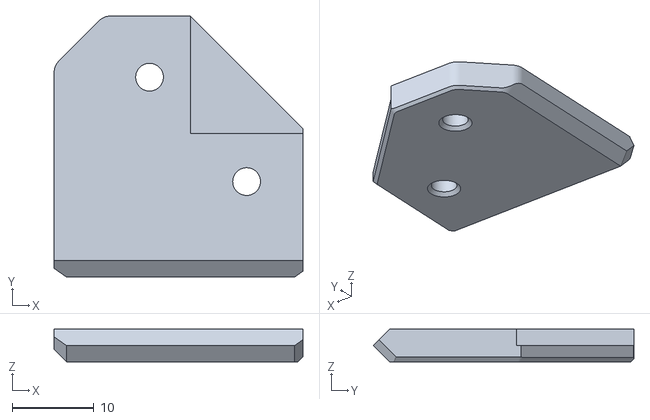
[picture p138: CAD file, 2021-03-21]
usermods/2020_Hinged_TopHat_Print/2020_Hinged_TopHat_Print_Top Rear Left Print.stl
30.5 x 32.0 x 4.00
