keithstrachan/Tiny-M/usermods/2020_Hinged_TopHat_Print/2020_Hinged_TopHat_Print_Hinge Top 2 Print.stl

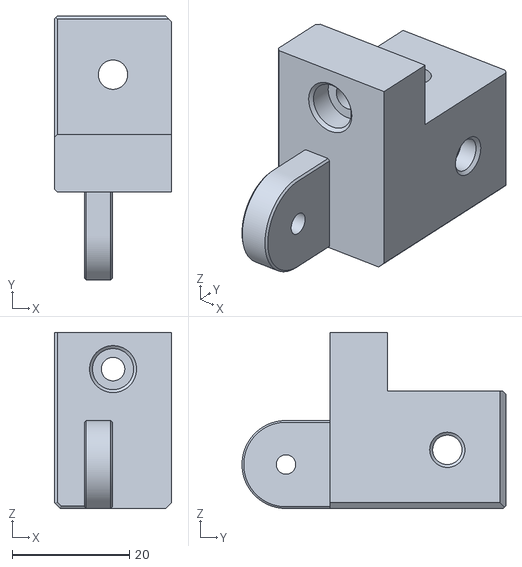
[picture p139: CAD file, 2021-03-21]
usermods/2020_Hinged_TopHat_Print/2020_Hinged_TopHat_Print_Hinge Top 2 Print.stl
20.0 x 45.0 x 30.0
